priimak/HaasoscopePro/sub boards/eval board/DC041A_ADC12DL3200EVM-ASY.pdf

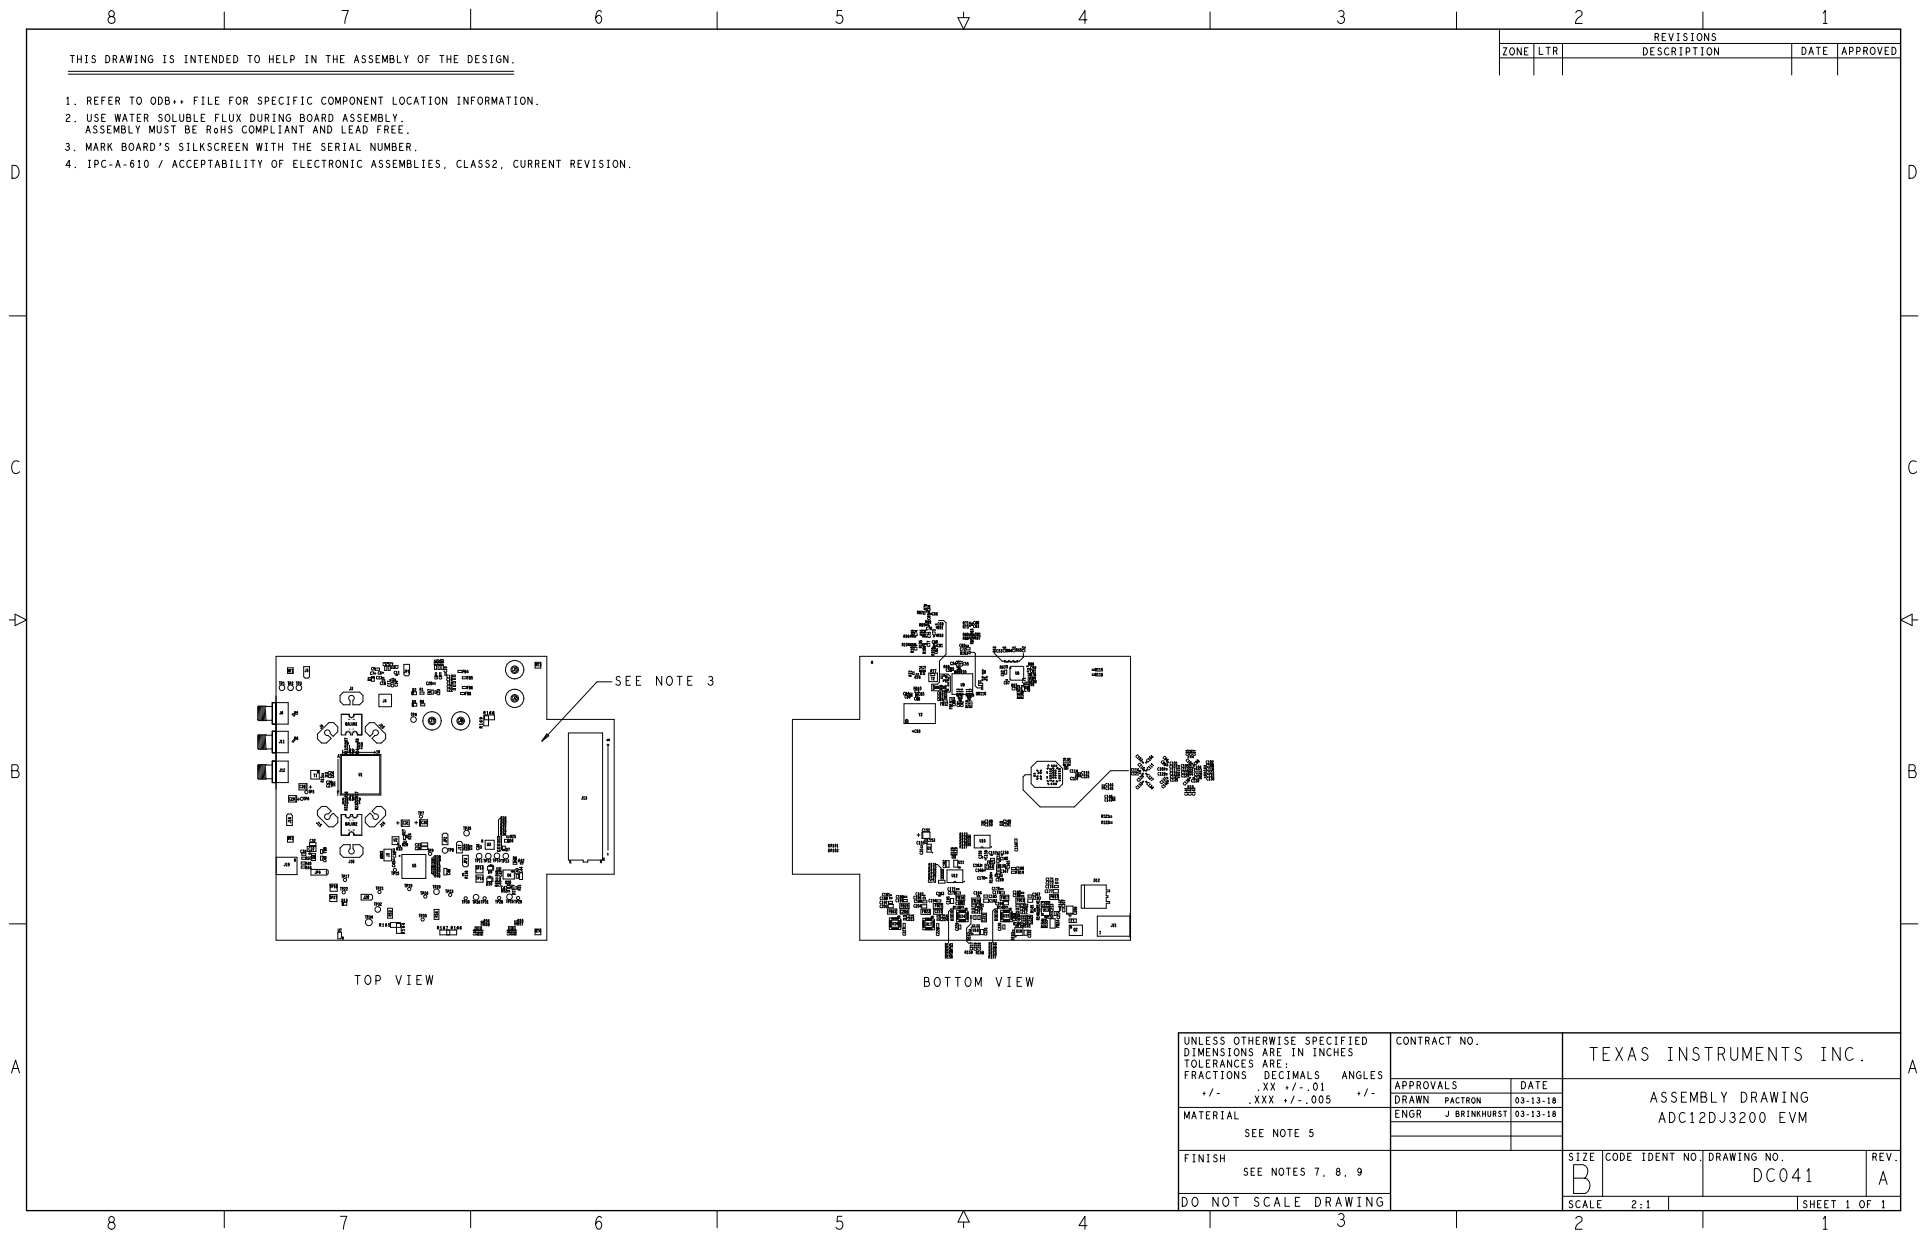
[picture p21: page 1]
