priimak/HaasoscopePro/sub boards/eval board/DC041A_ADC12DL3200EVM-FAB.pdf

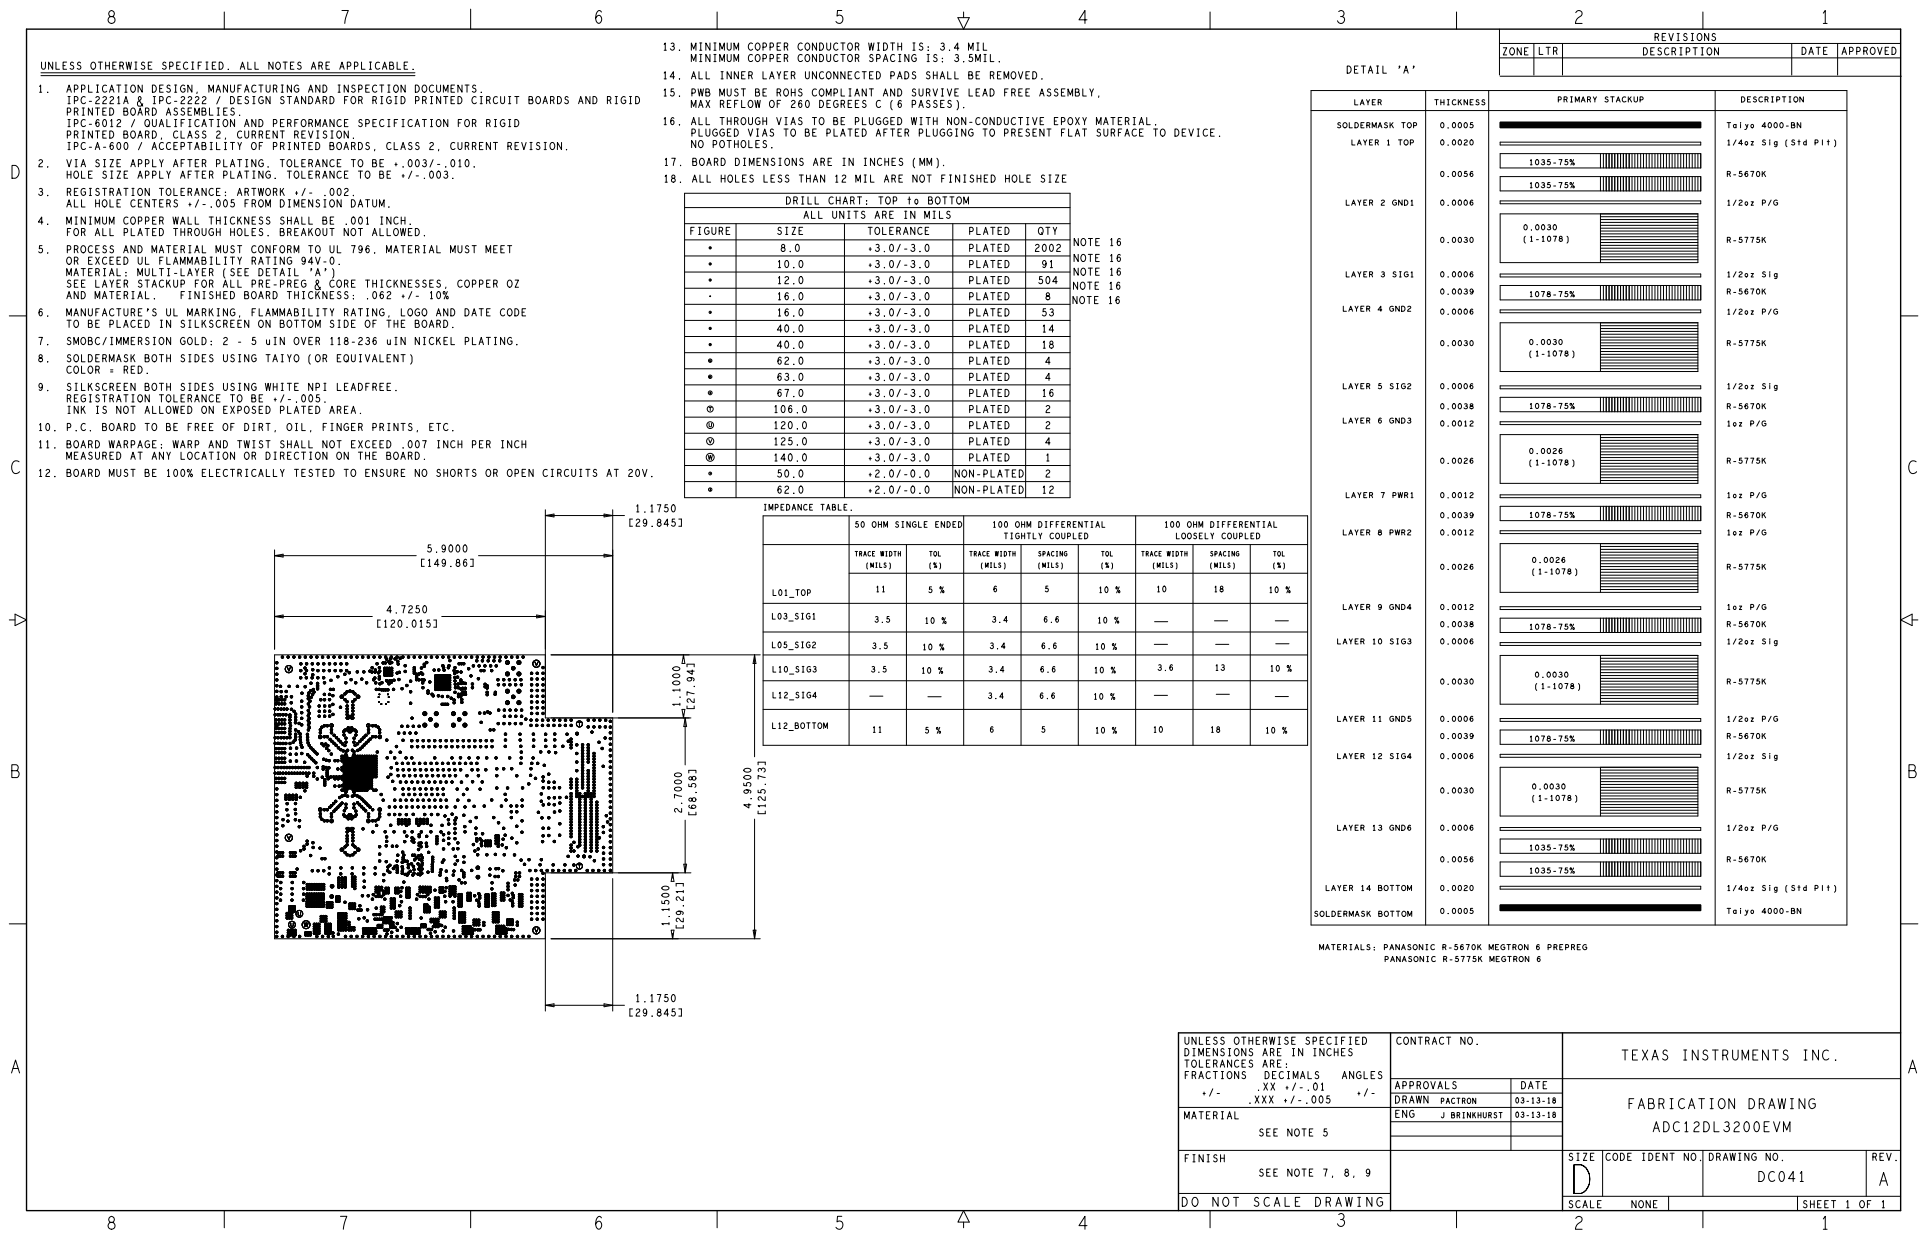
[picture p22: page 1]
