priimak/HaasoscopePro/sub boards/eval board/DC041A_ADC12DL3200EVM-LYR.pdf

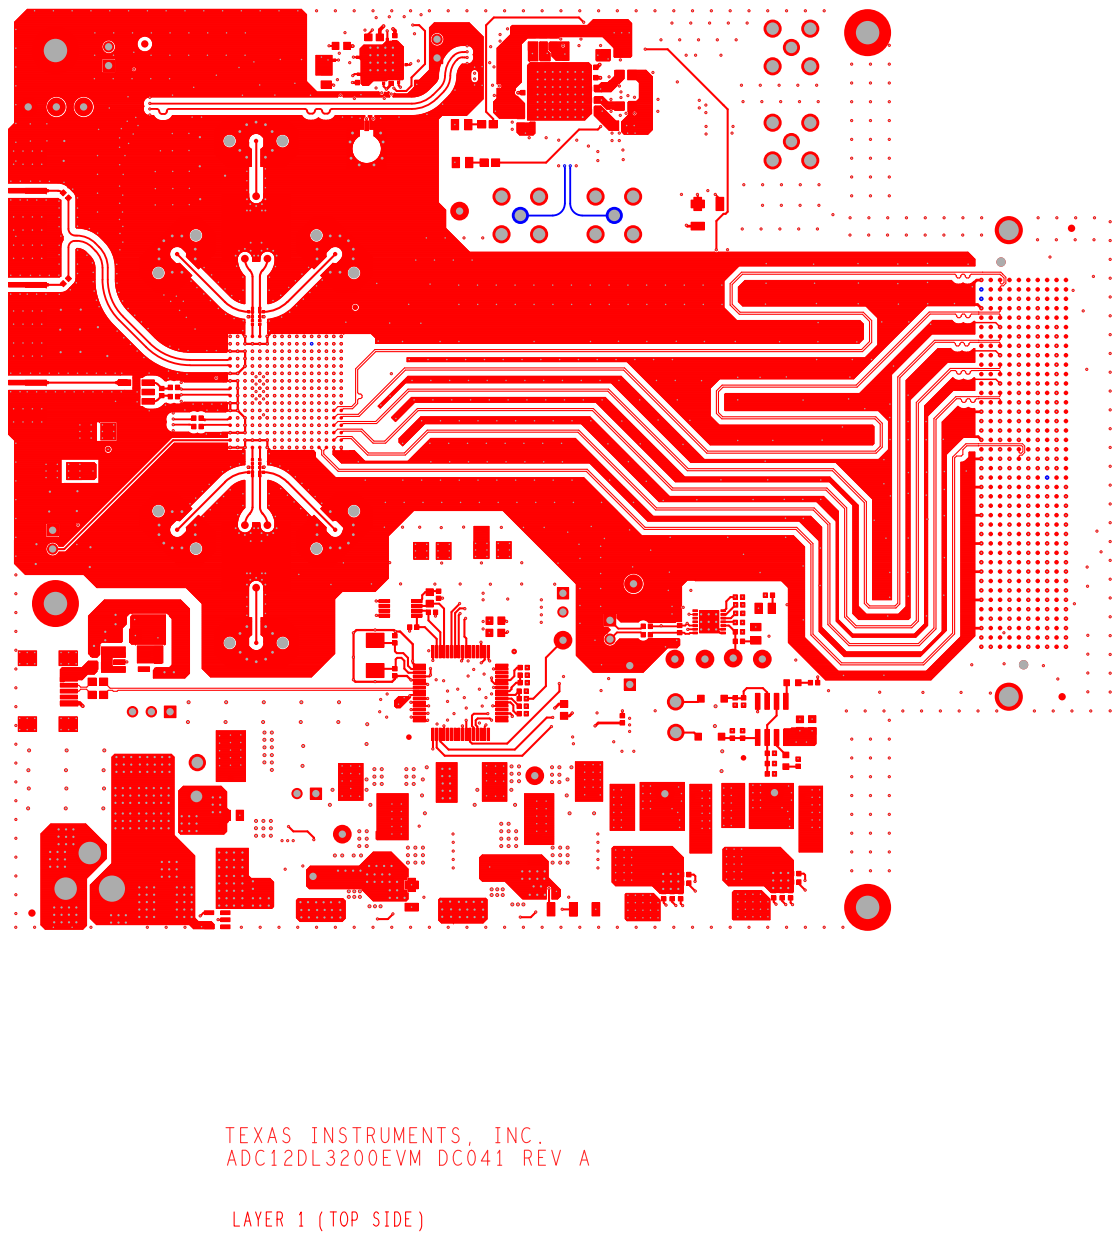
[picture p23: page 1]

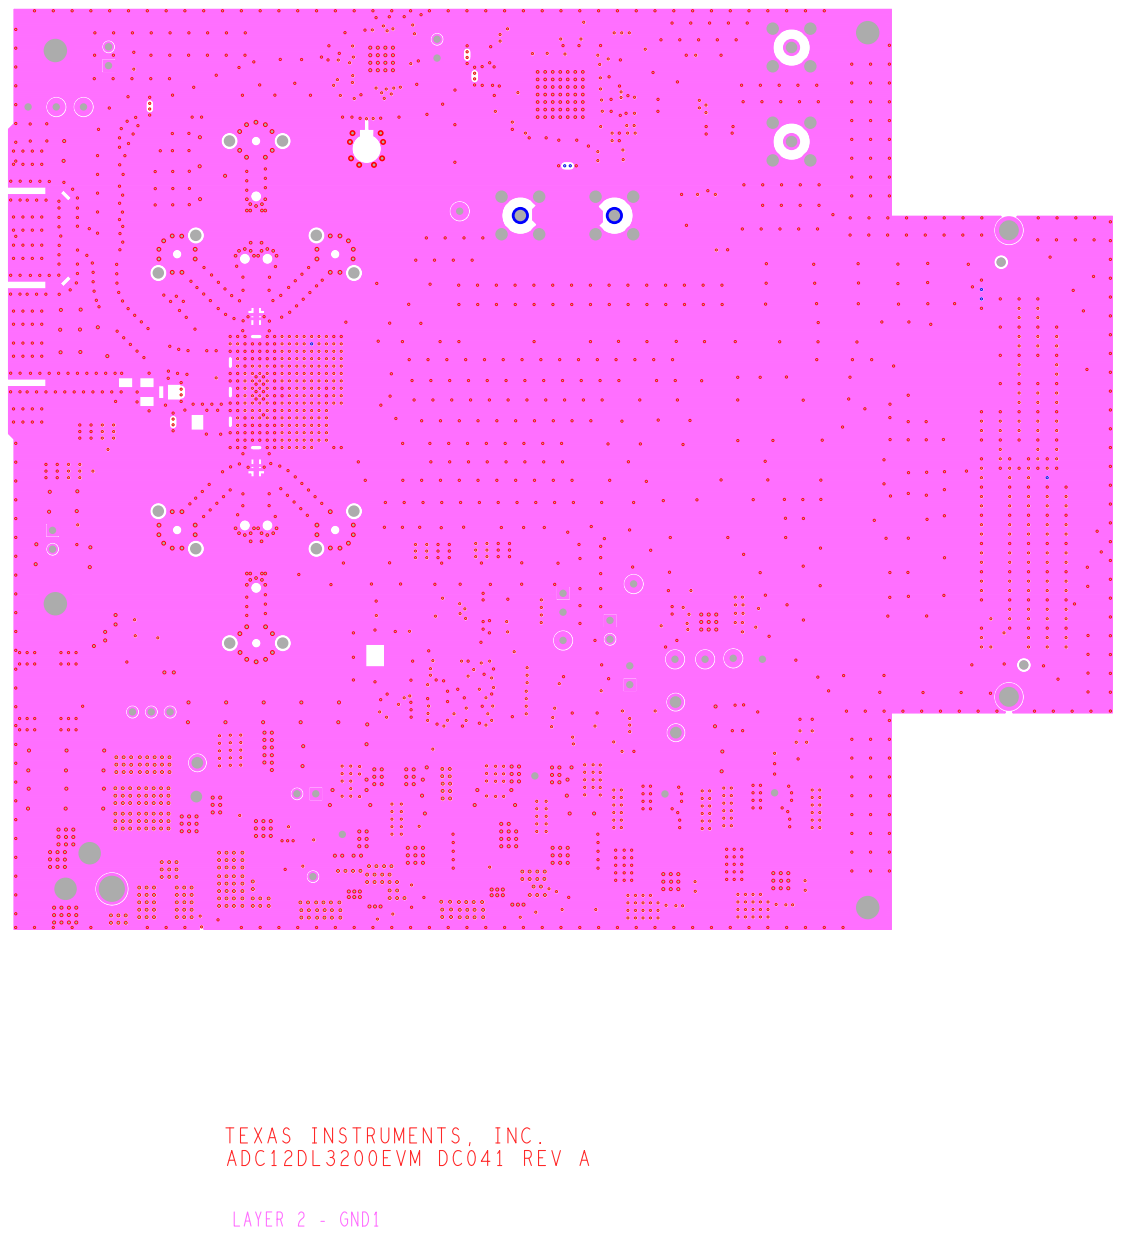
[picture p24: page 2]

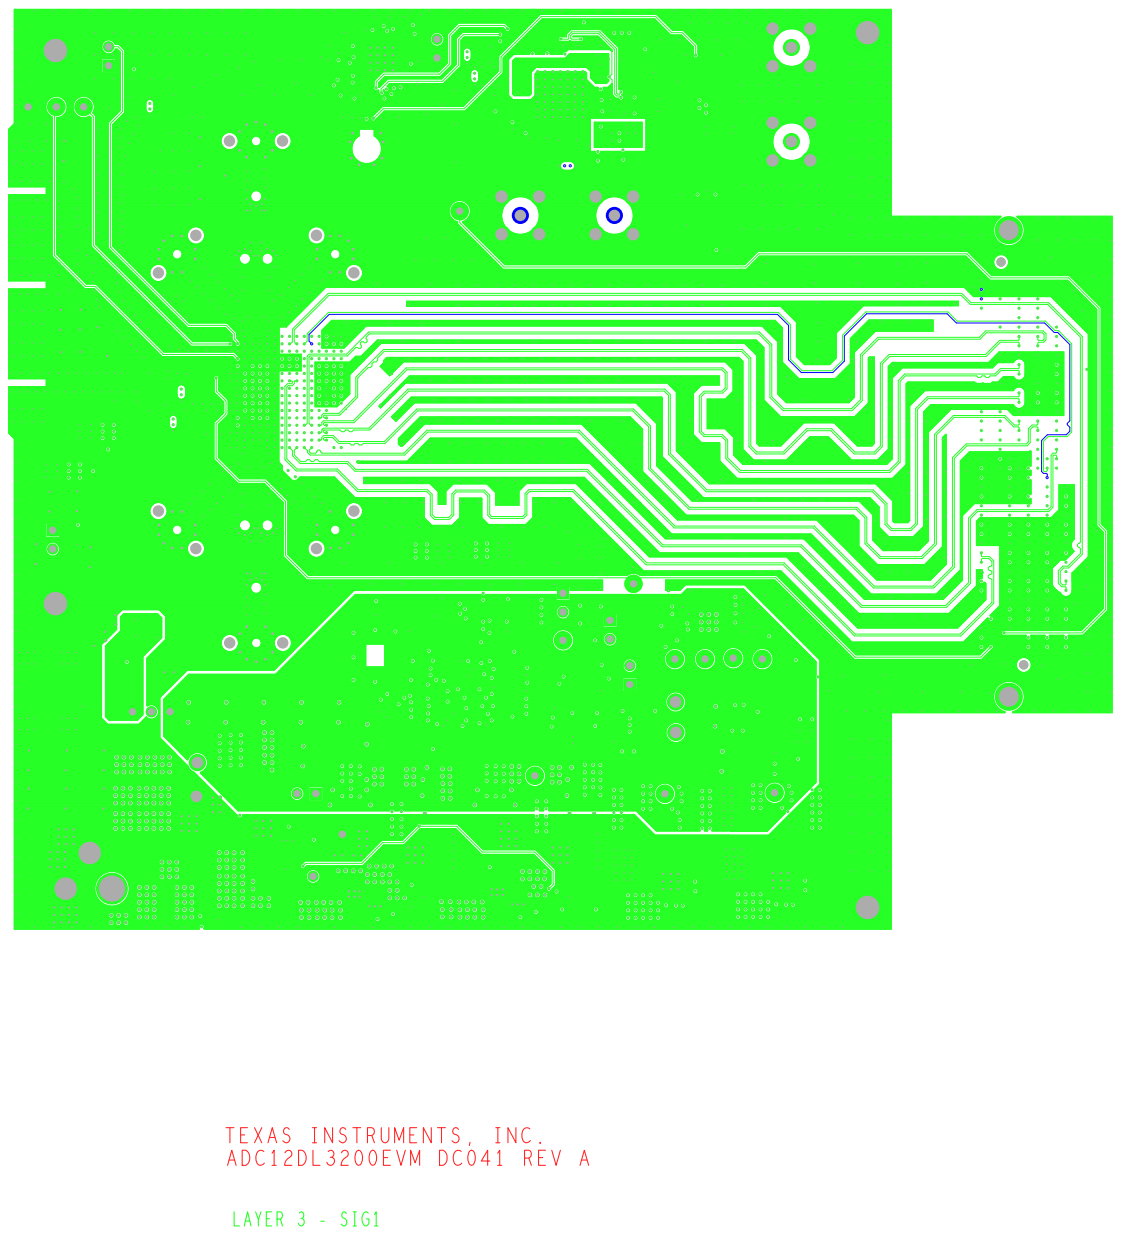
[picture p25: page 3]

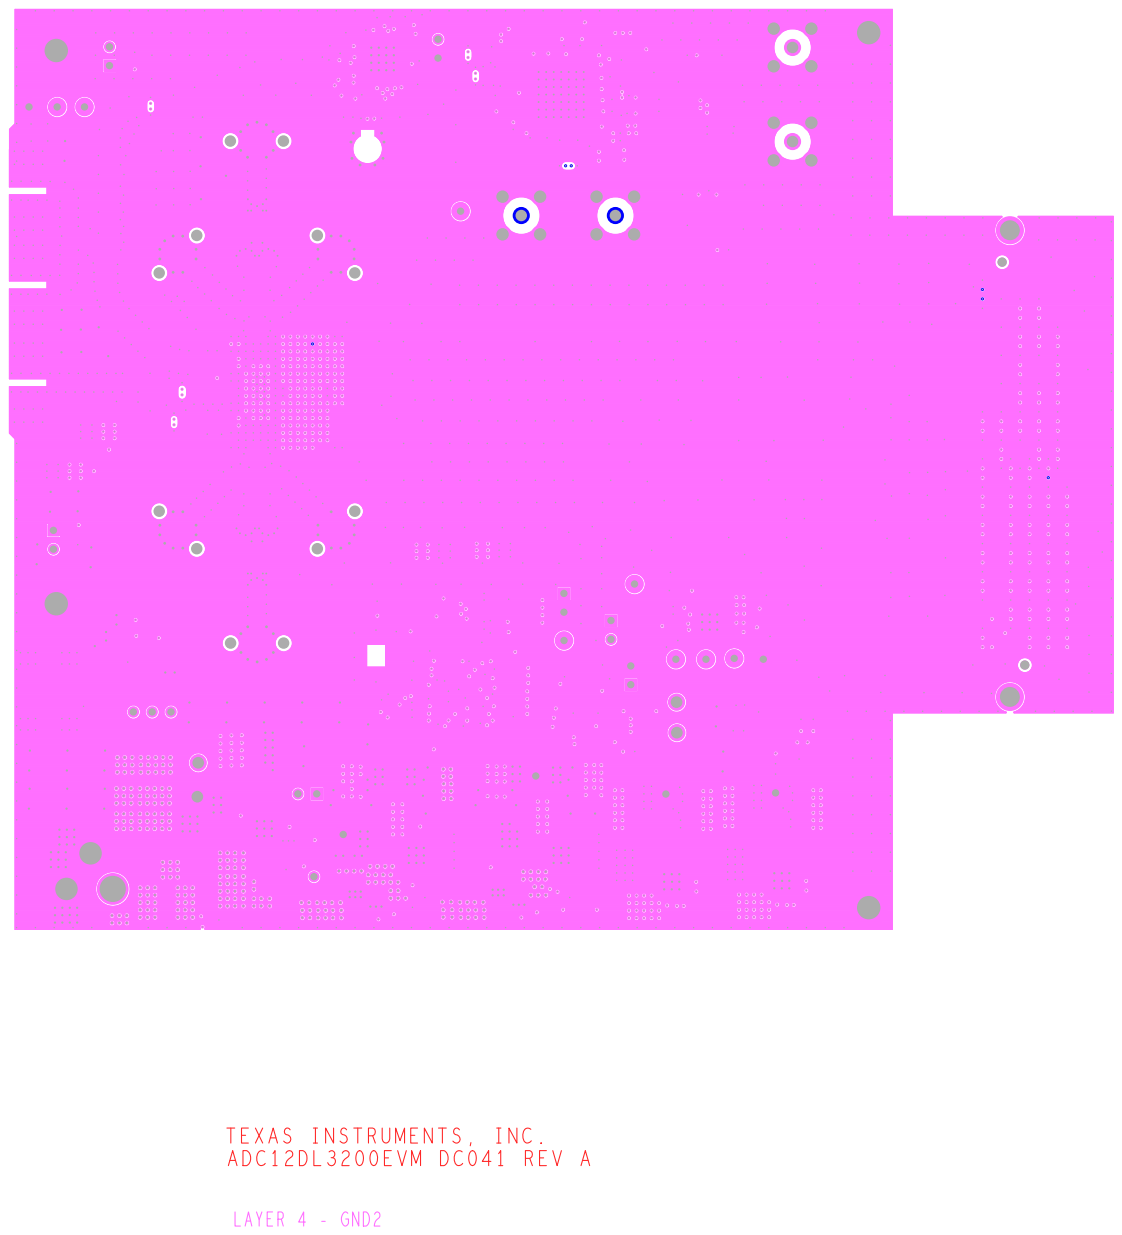
[picture p26: page 4]

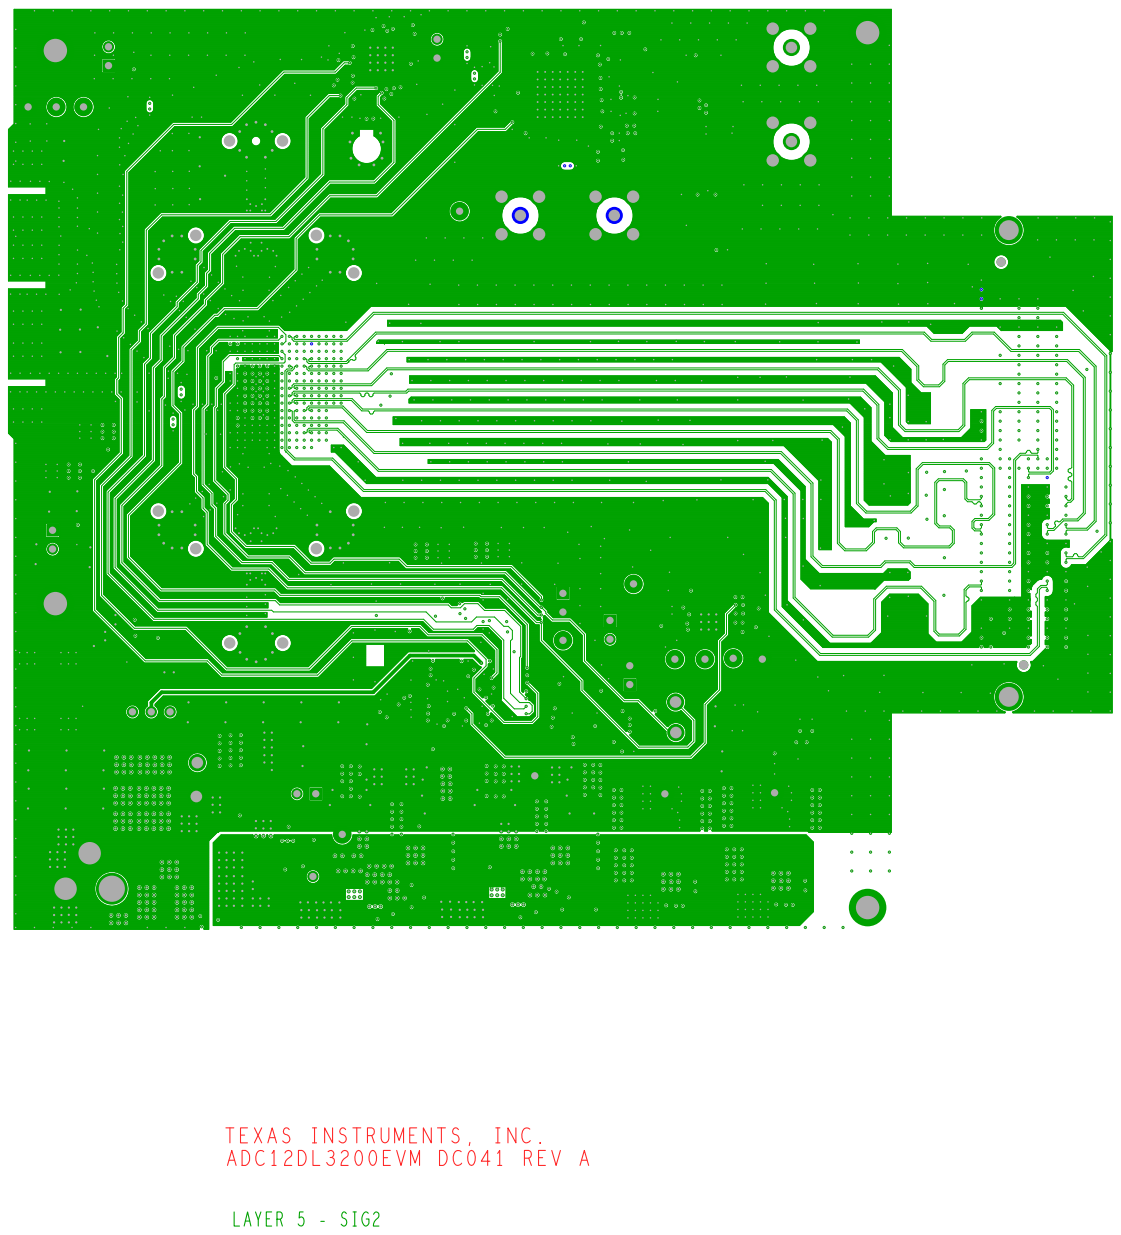
[picture p27: page 5]

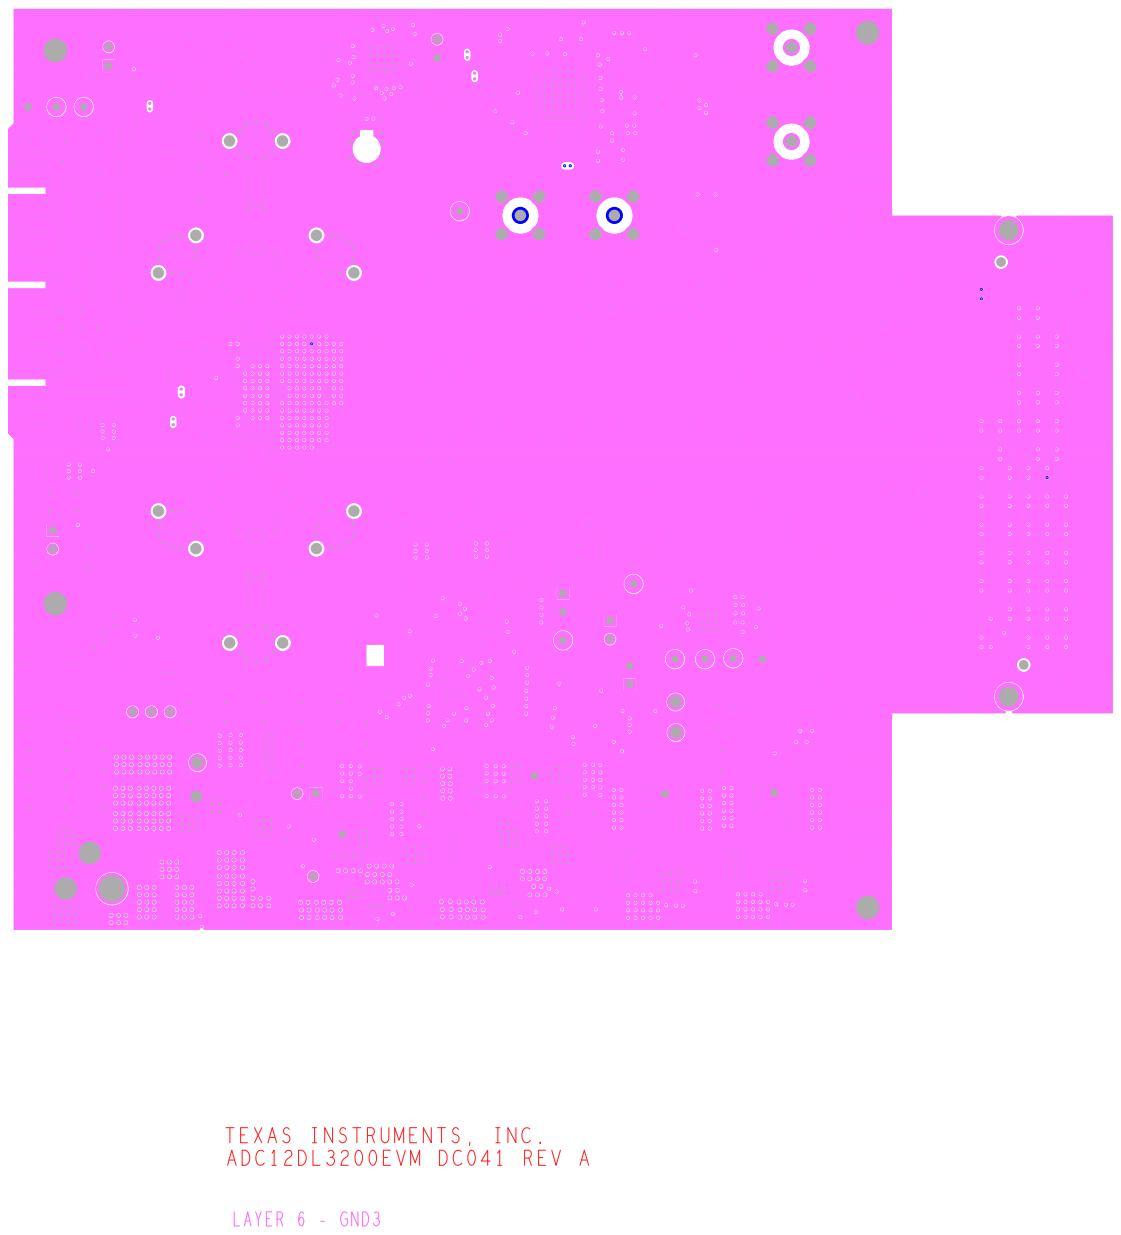
[picture p28: page 6]

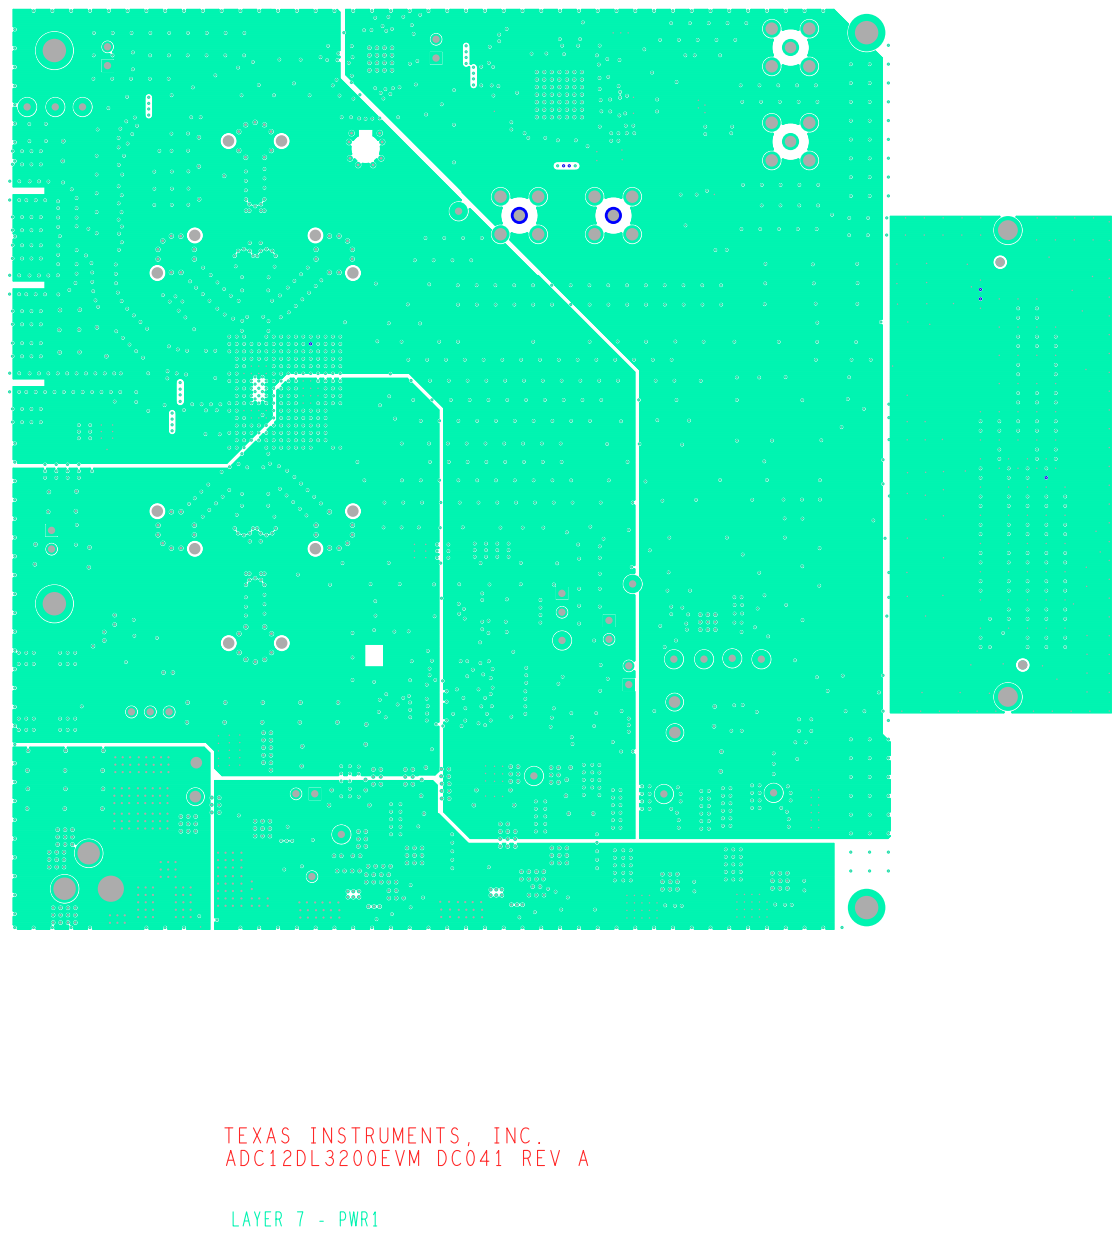
[picture p29: page 7]

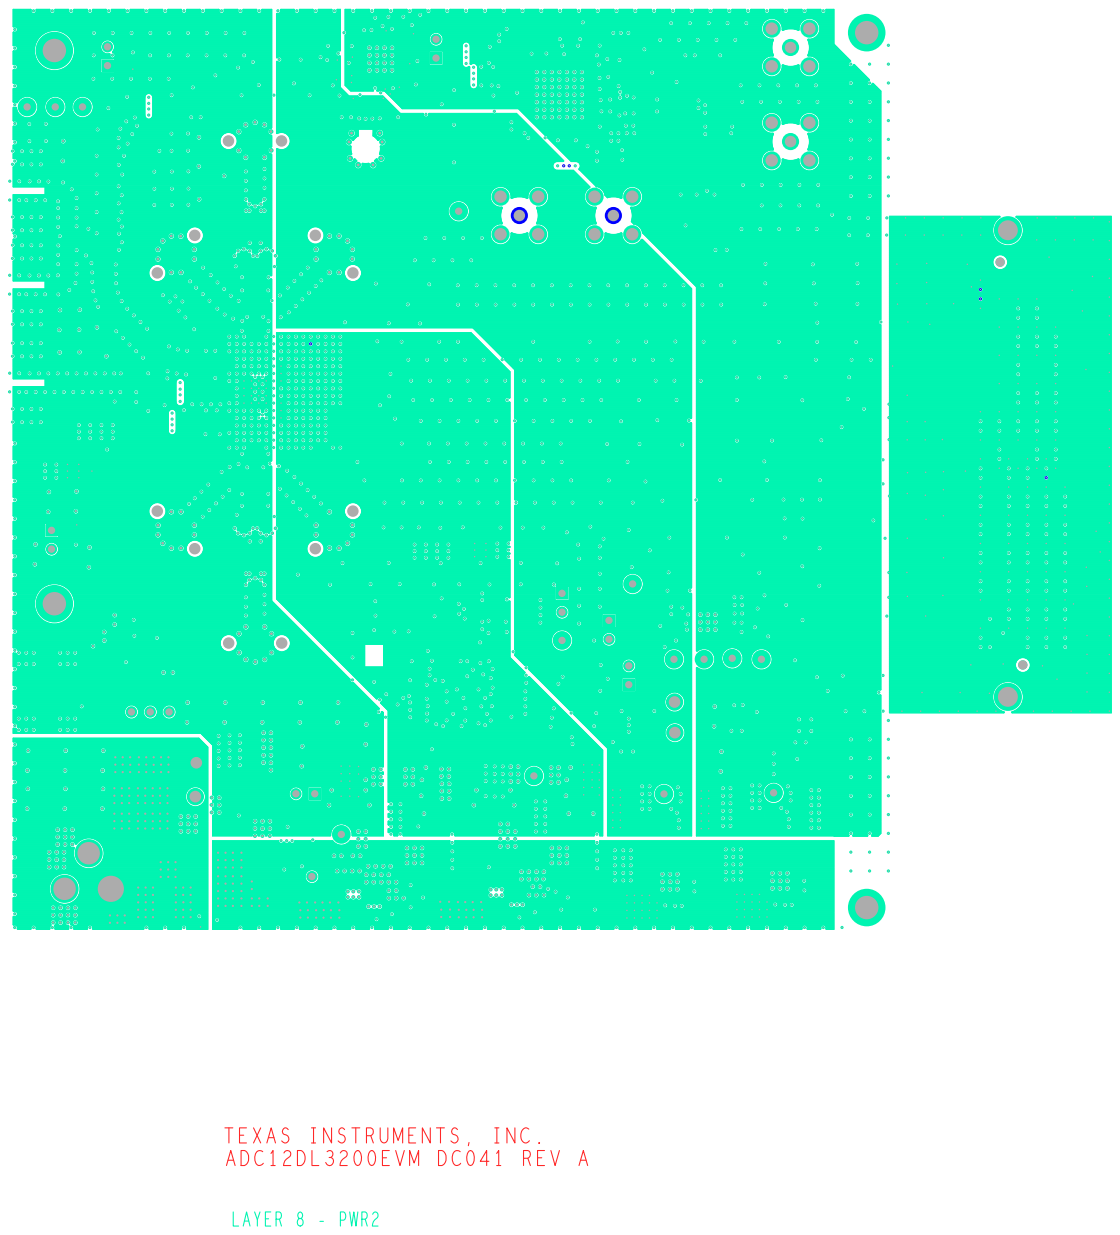
[picture p30: page 8]

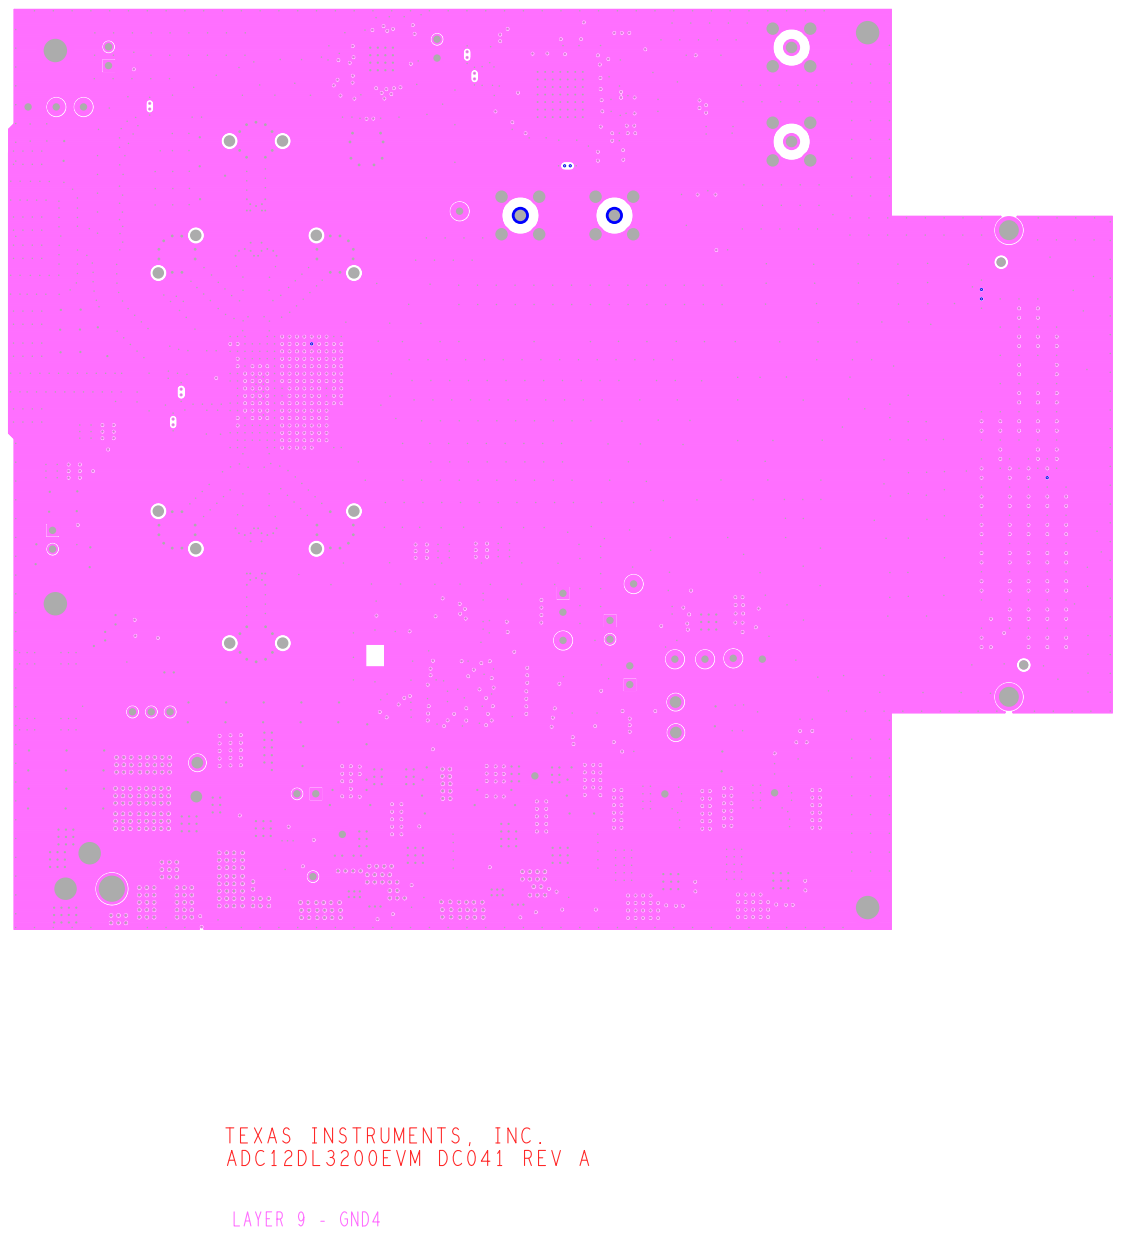
[picture p31: page 9]

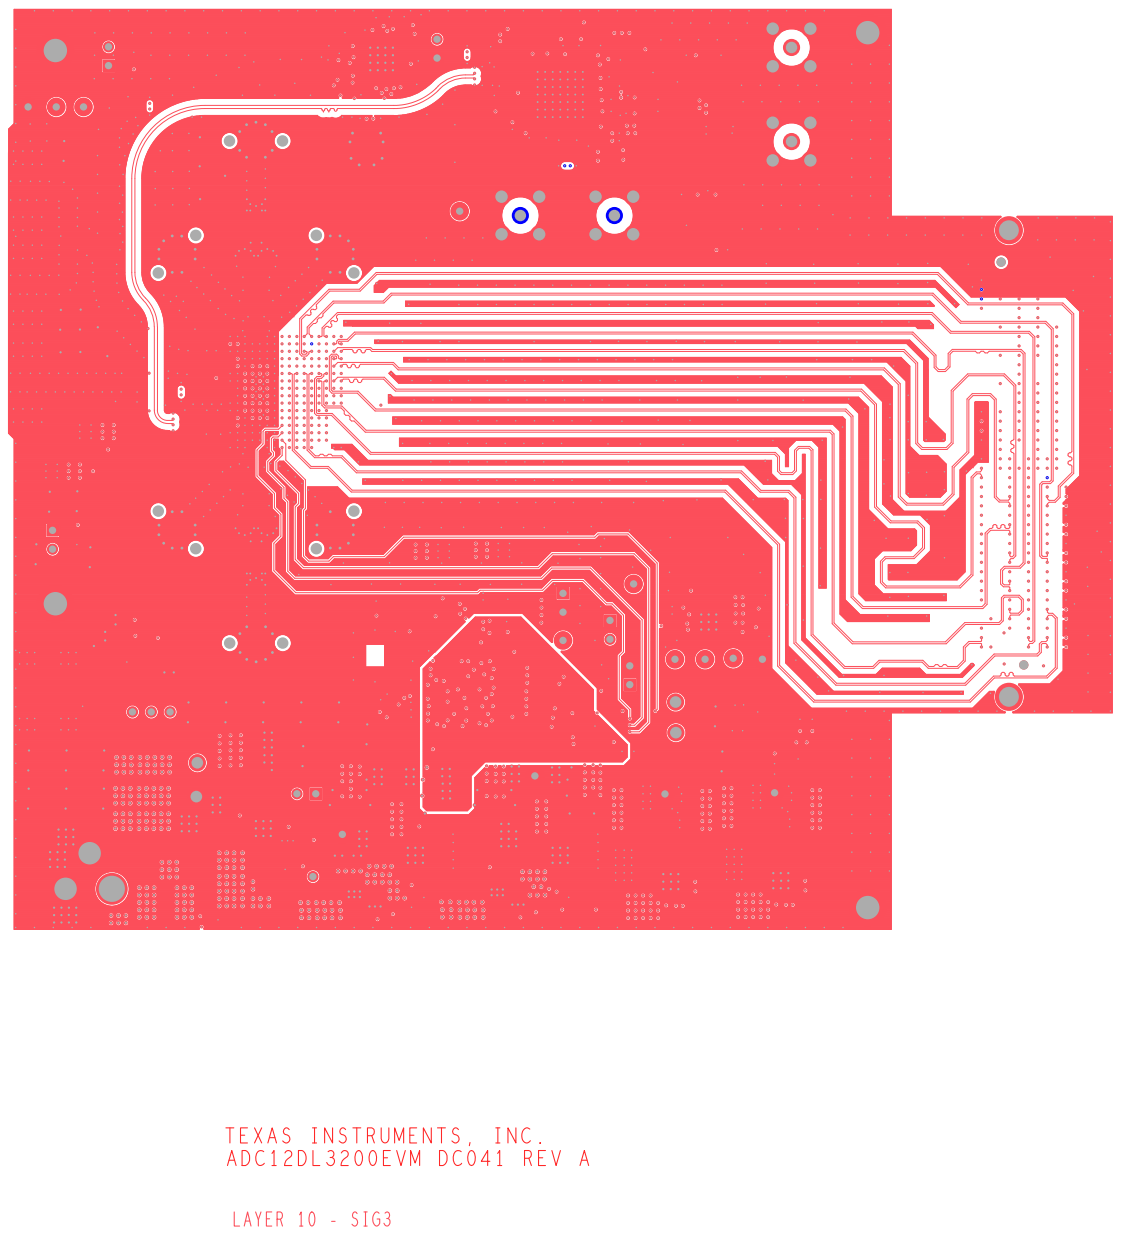
[picture p32: page 10]

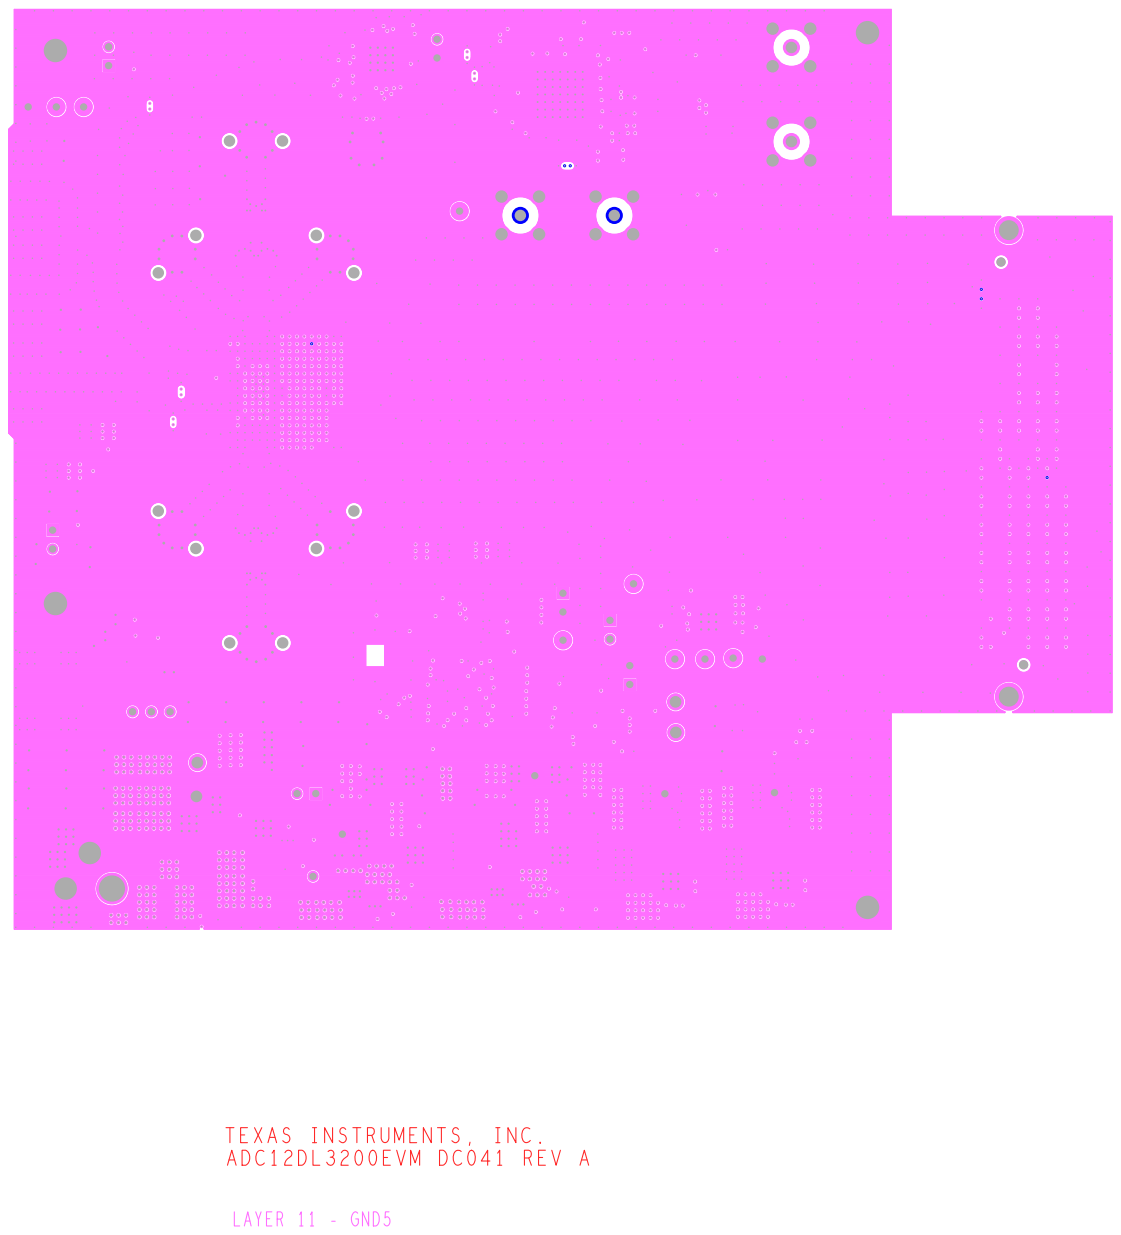
[picture p33: page 11]

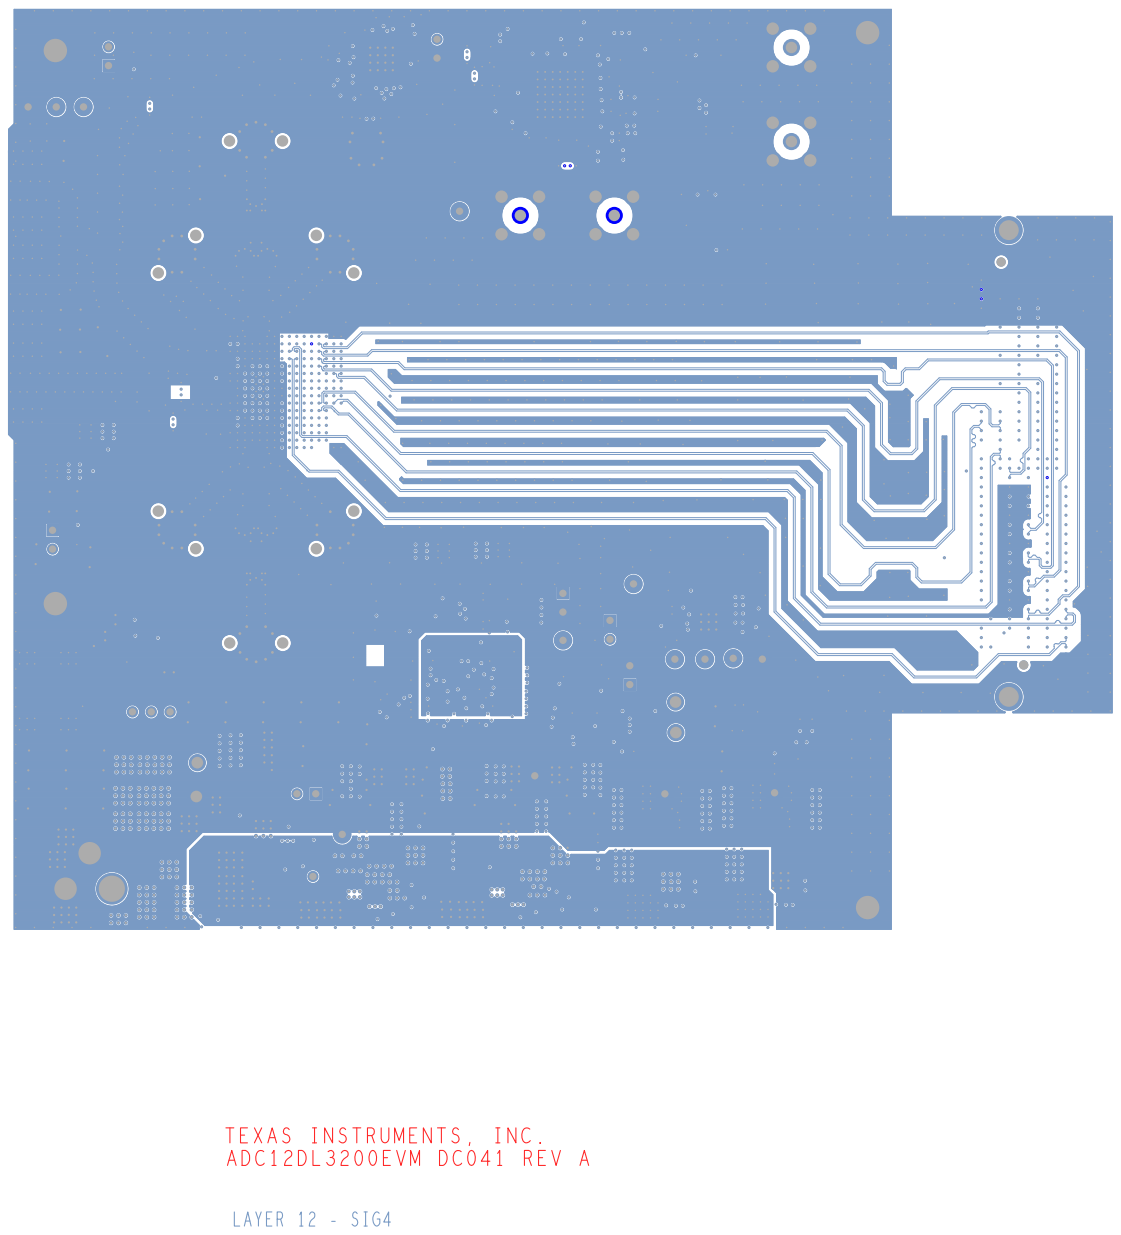
[picture p34: page 12]

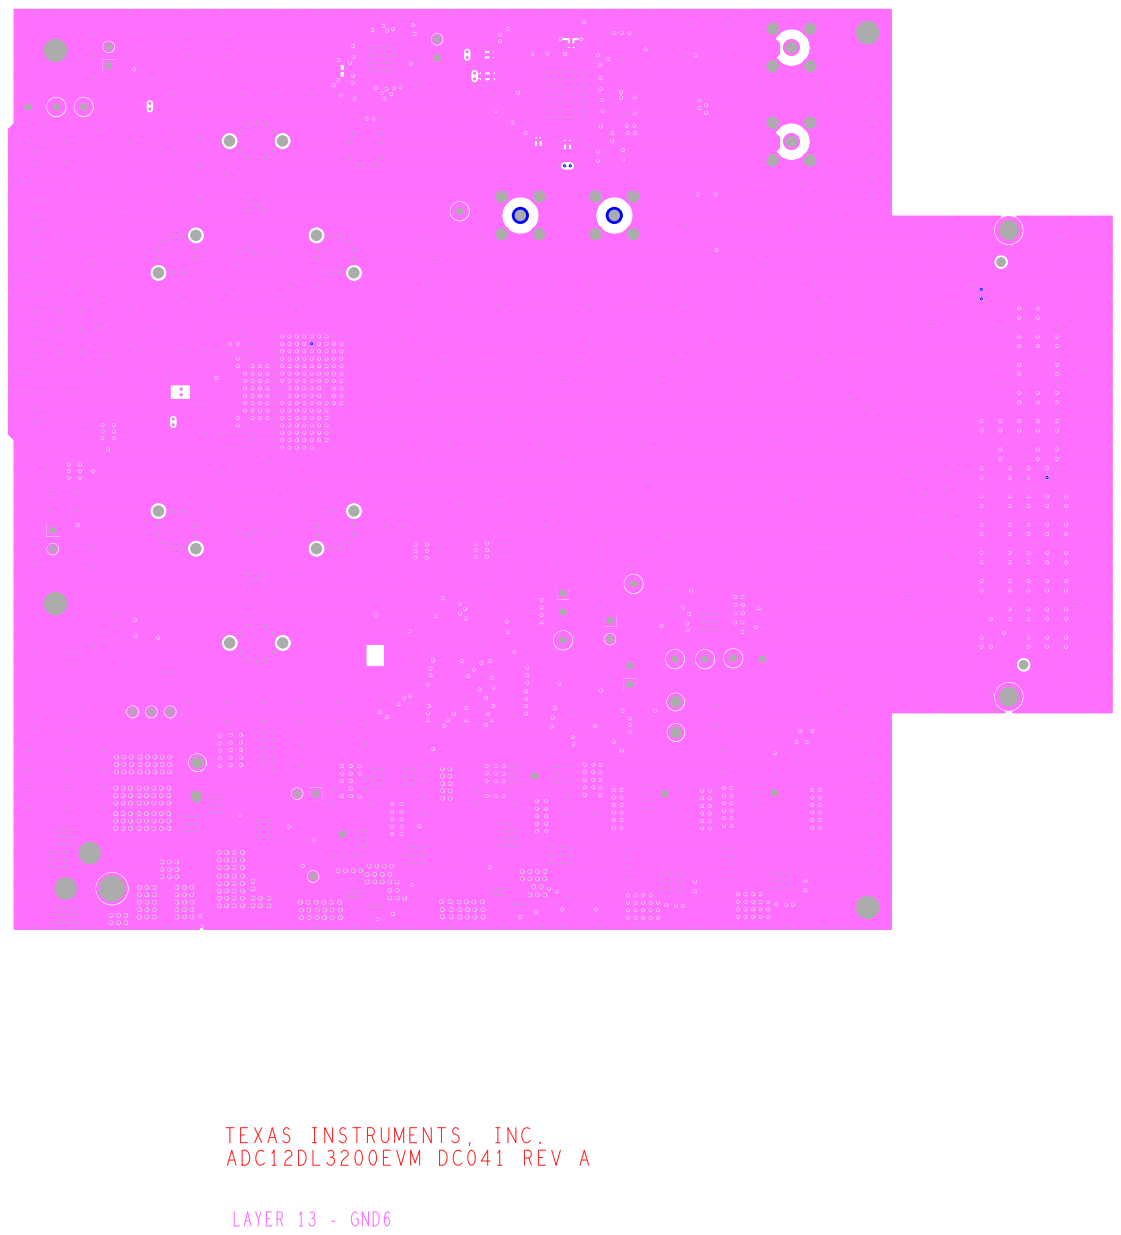
[picture p35: page 13]

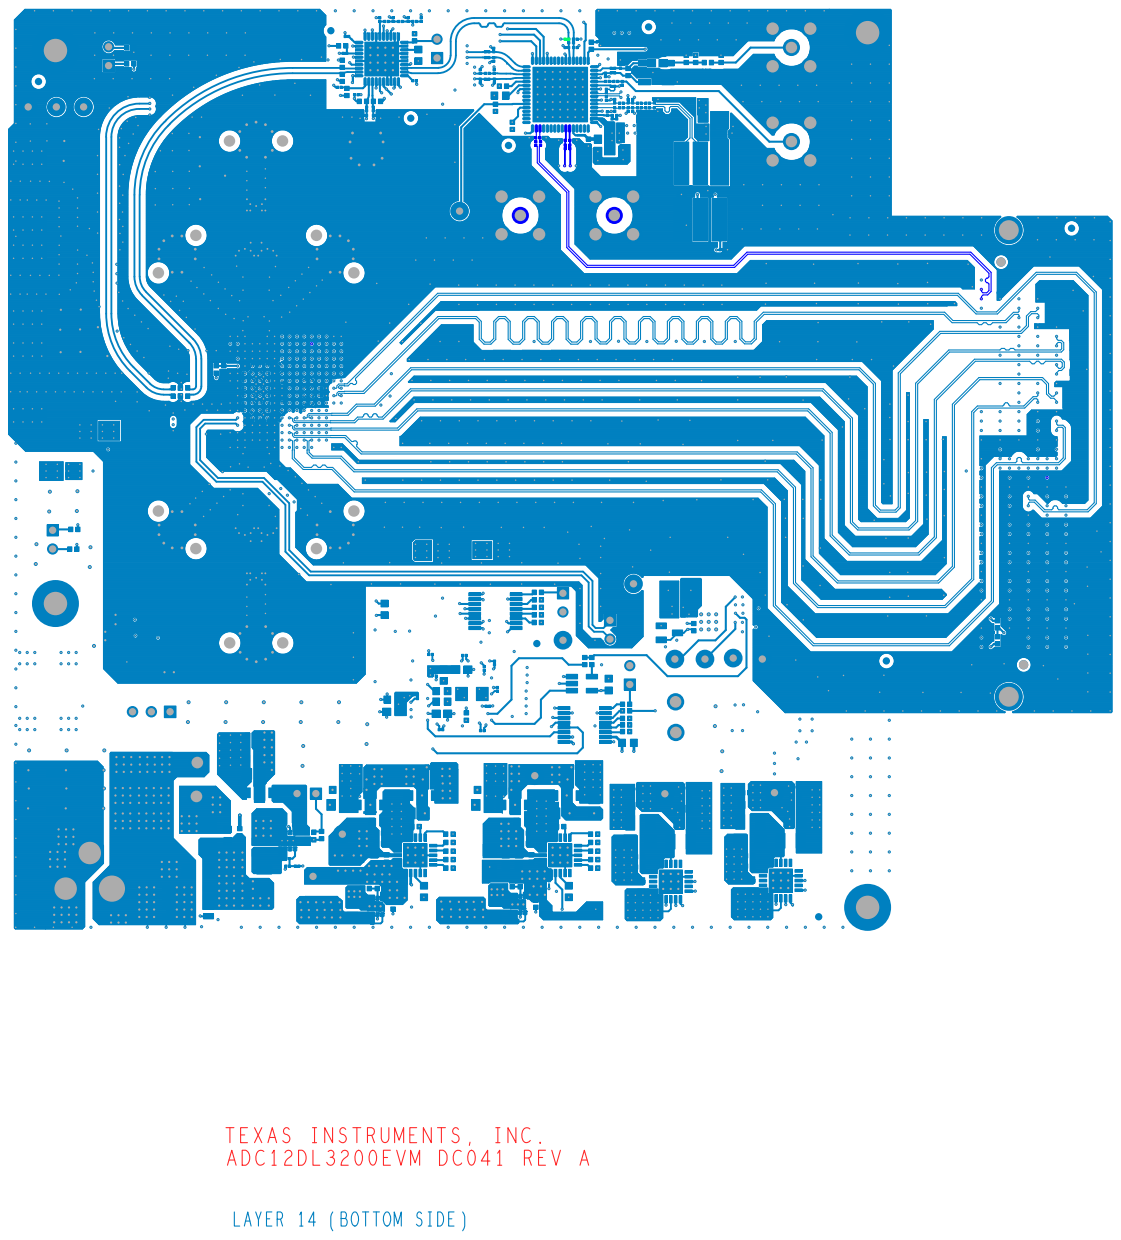
[picture p36: page 14]

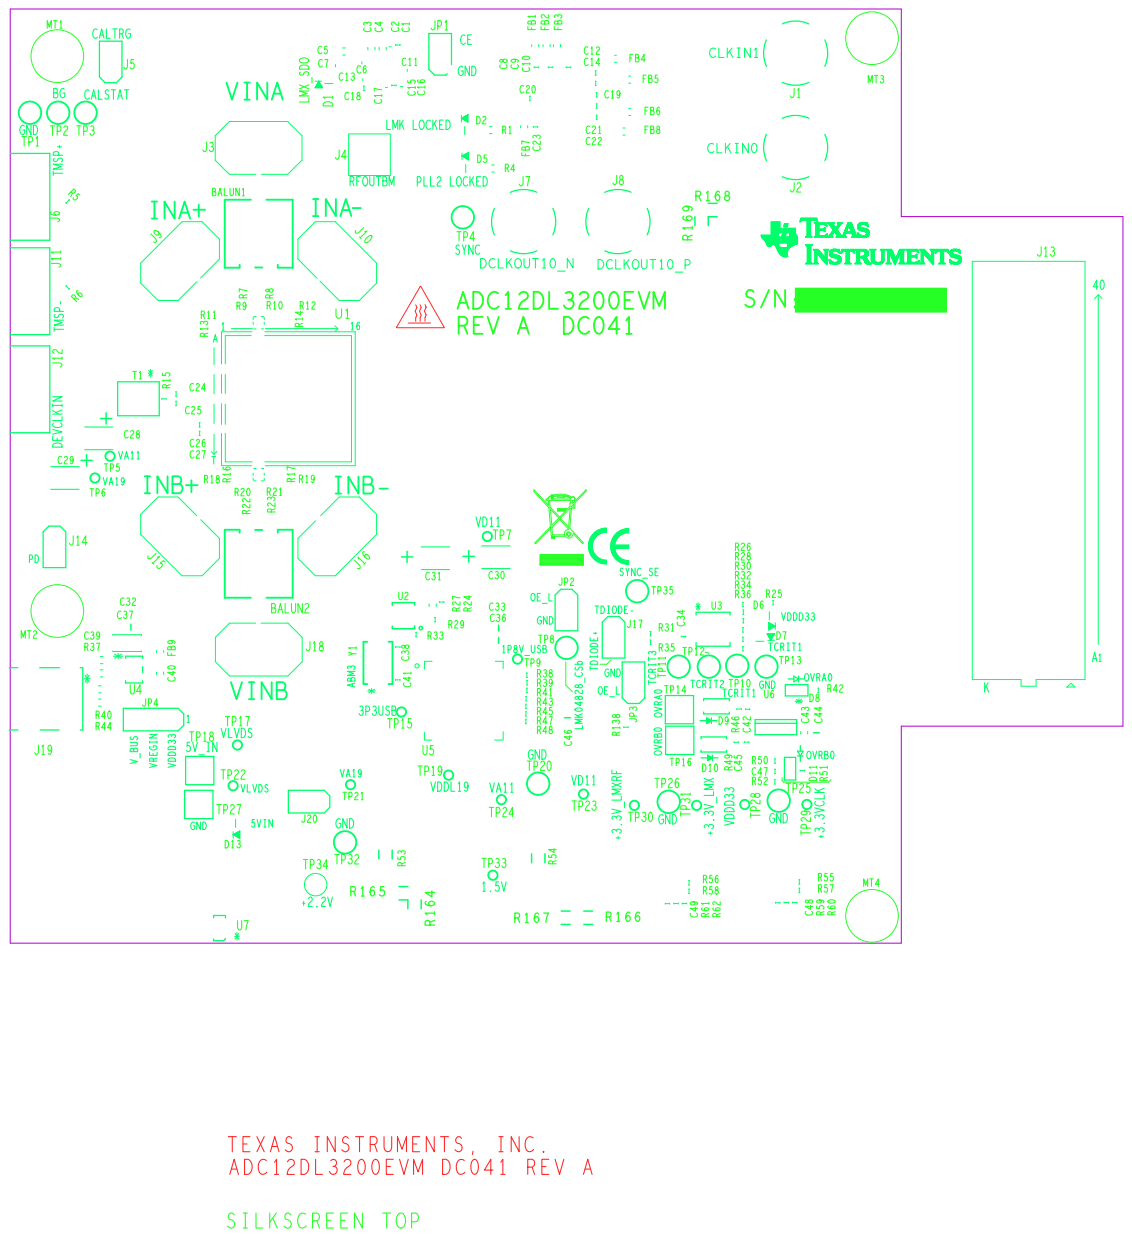
[picture p37: page 15]

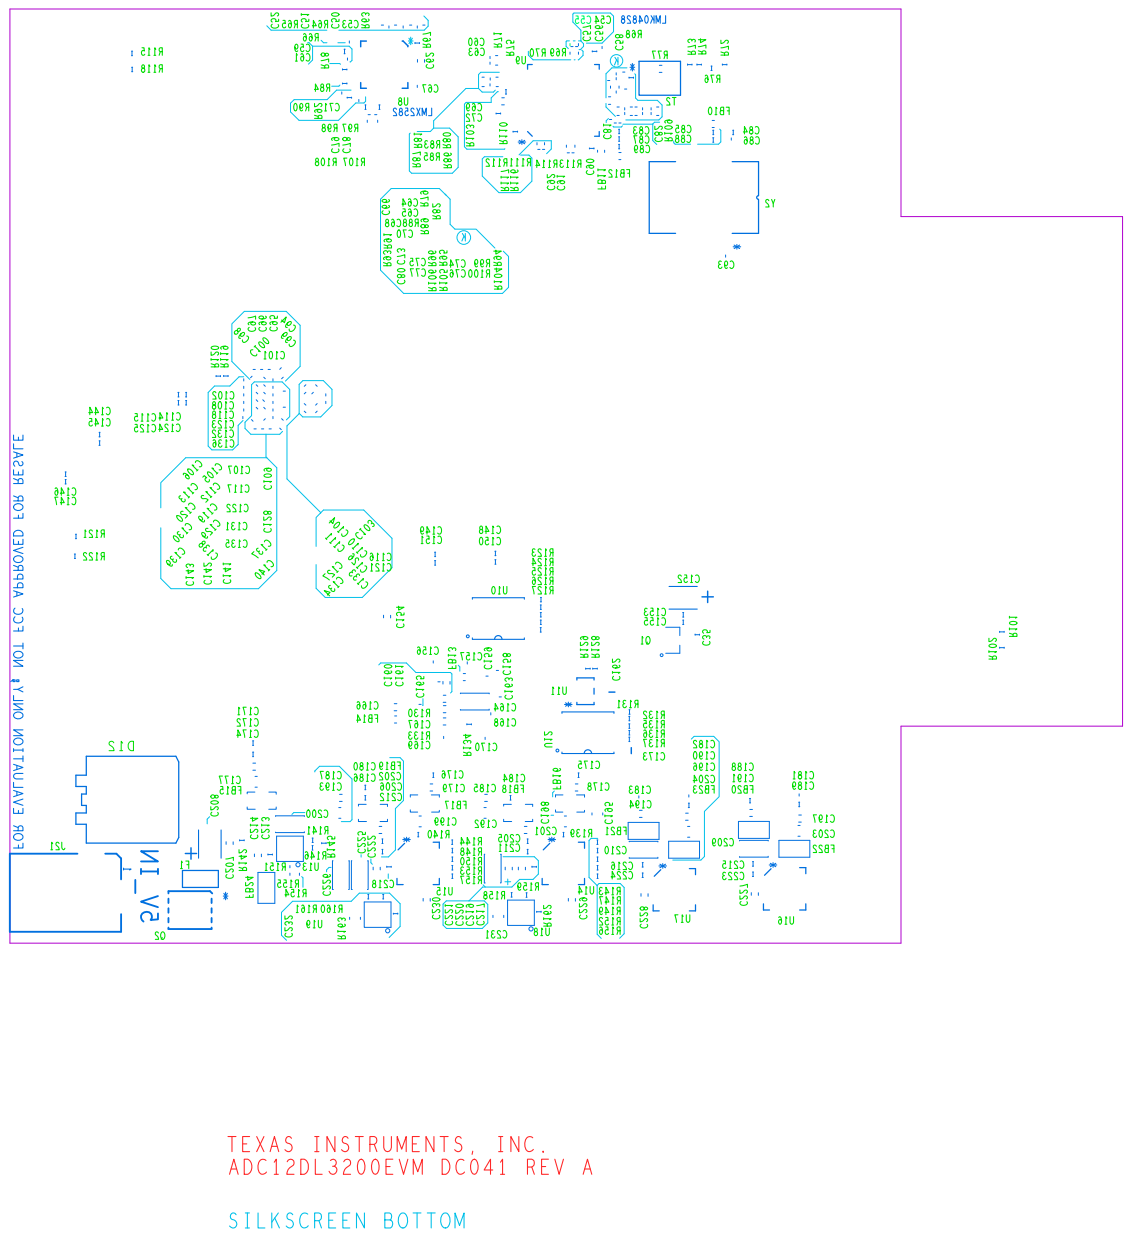
[picture p38: page 16]

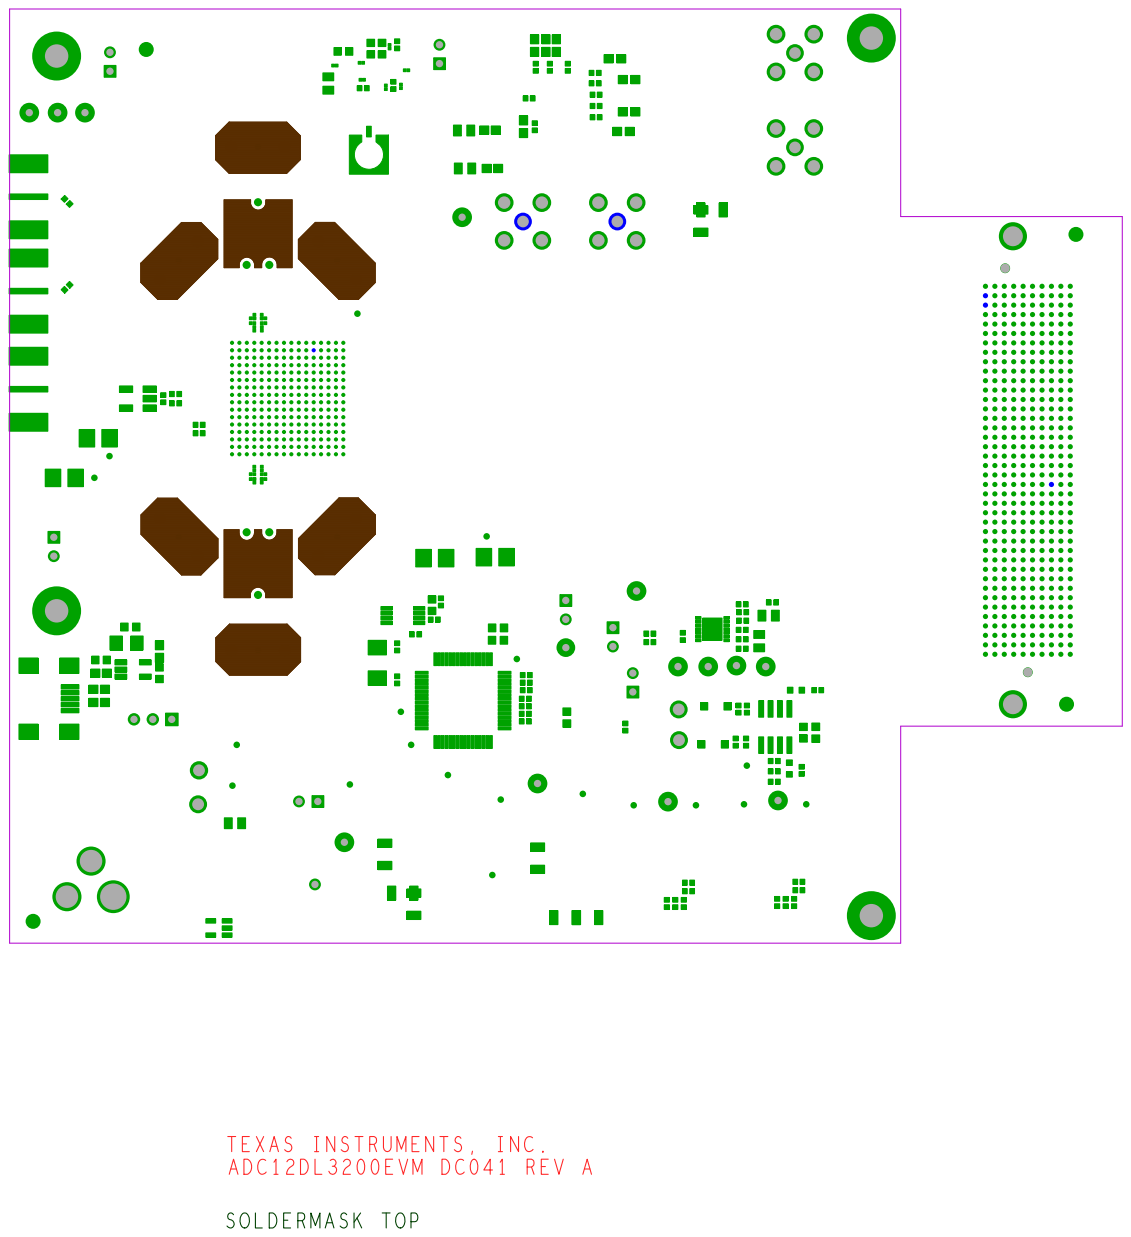
[picture p39: page 17]

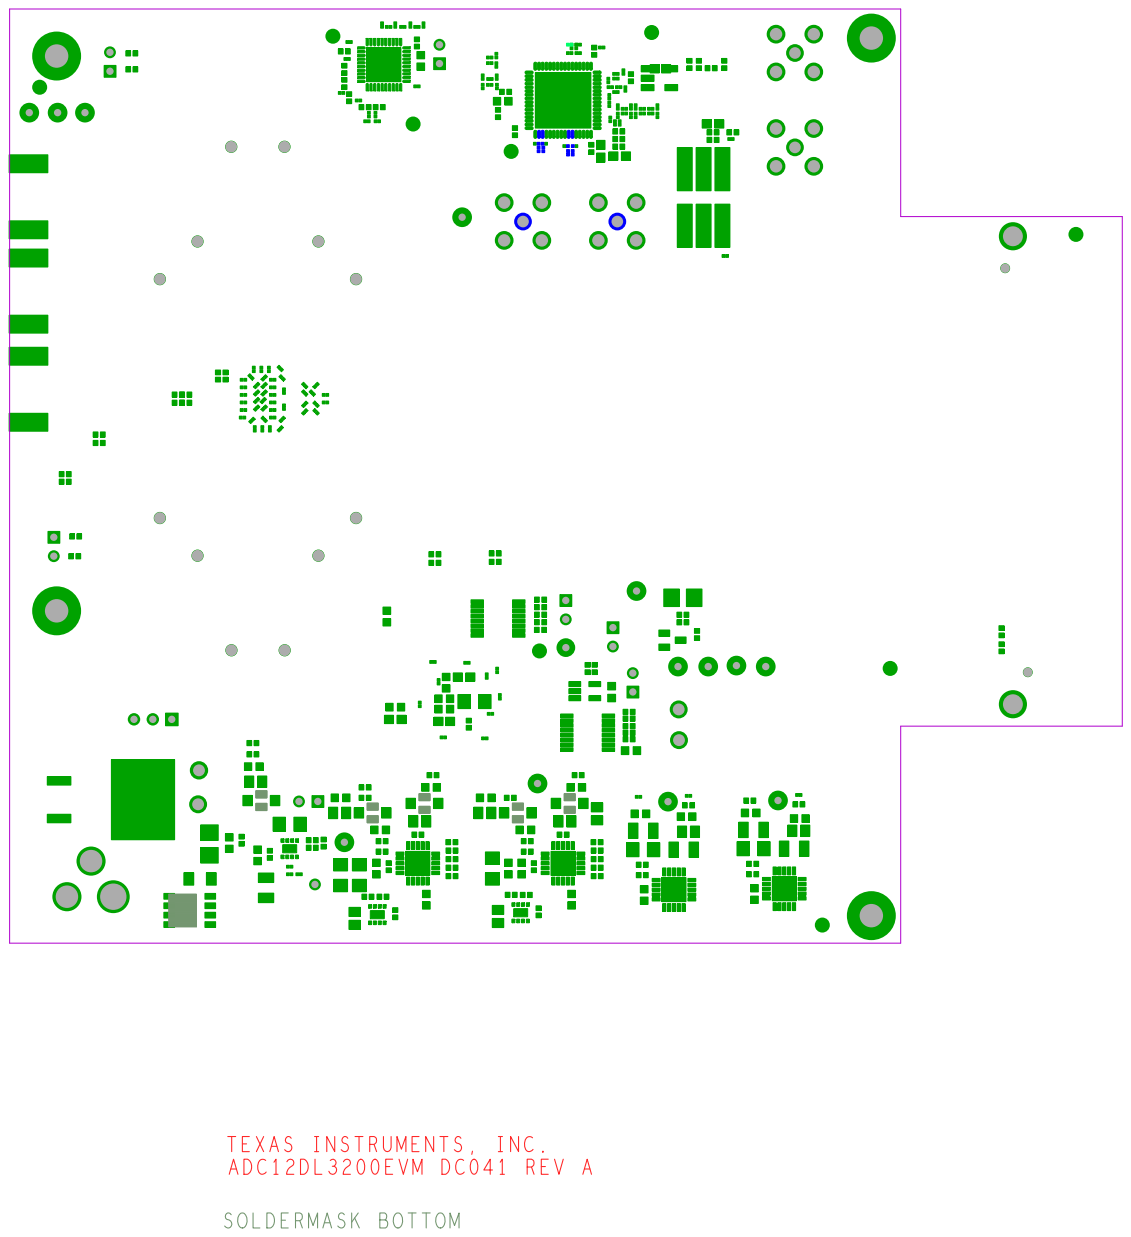
[picture p40: page 18]

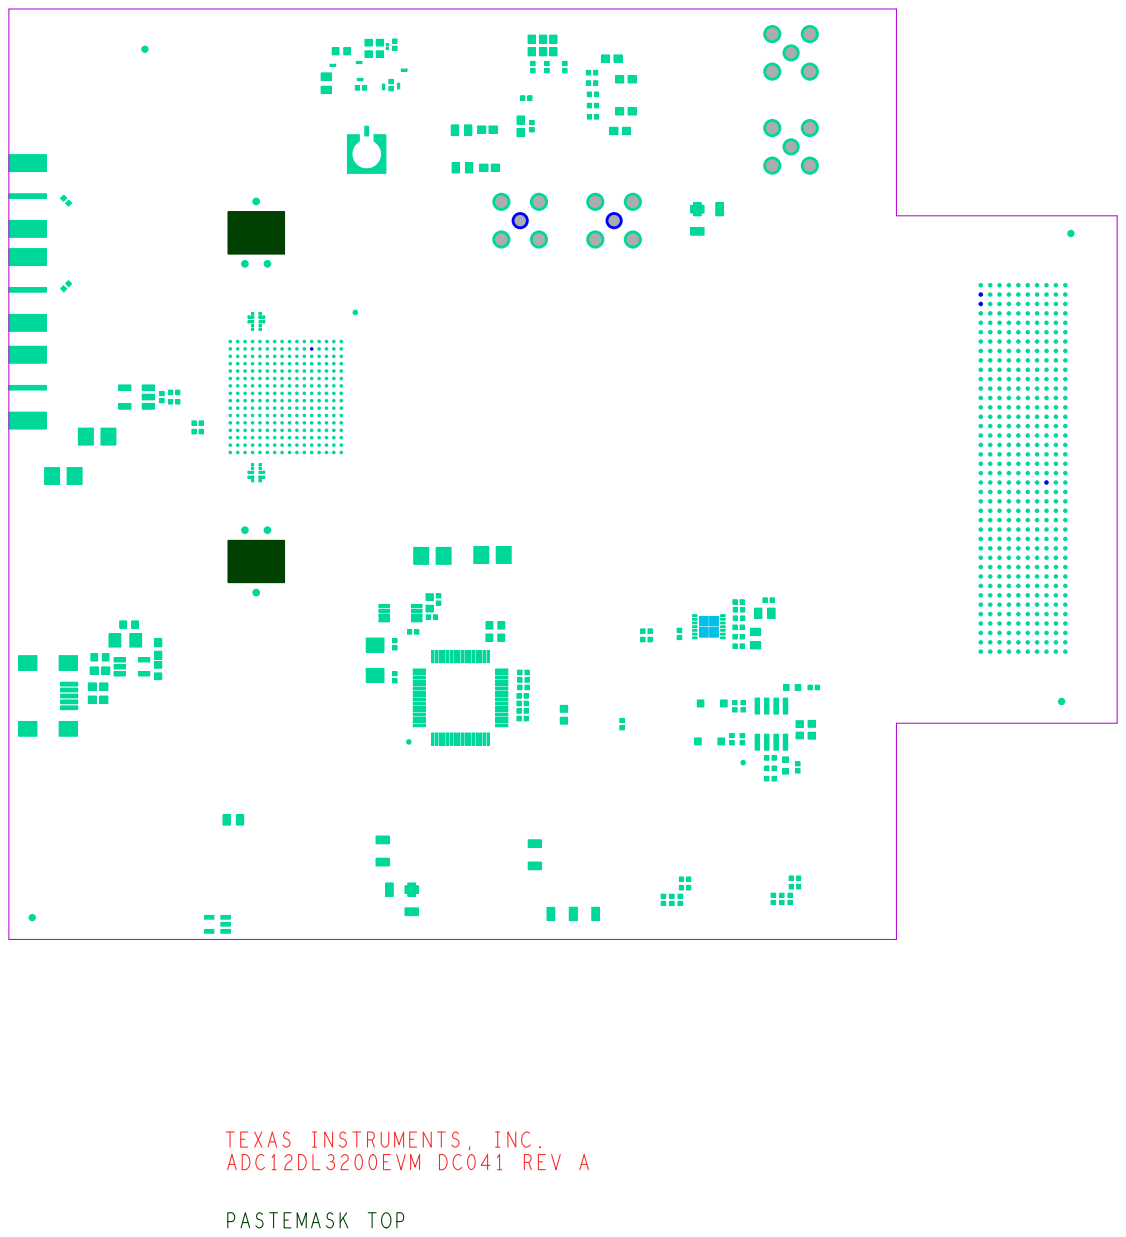
[picture p41: page 19]

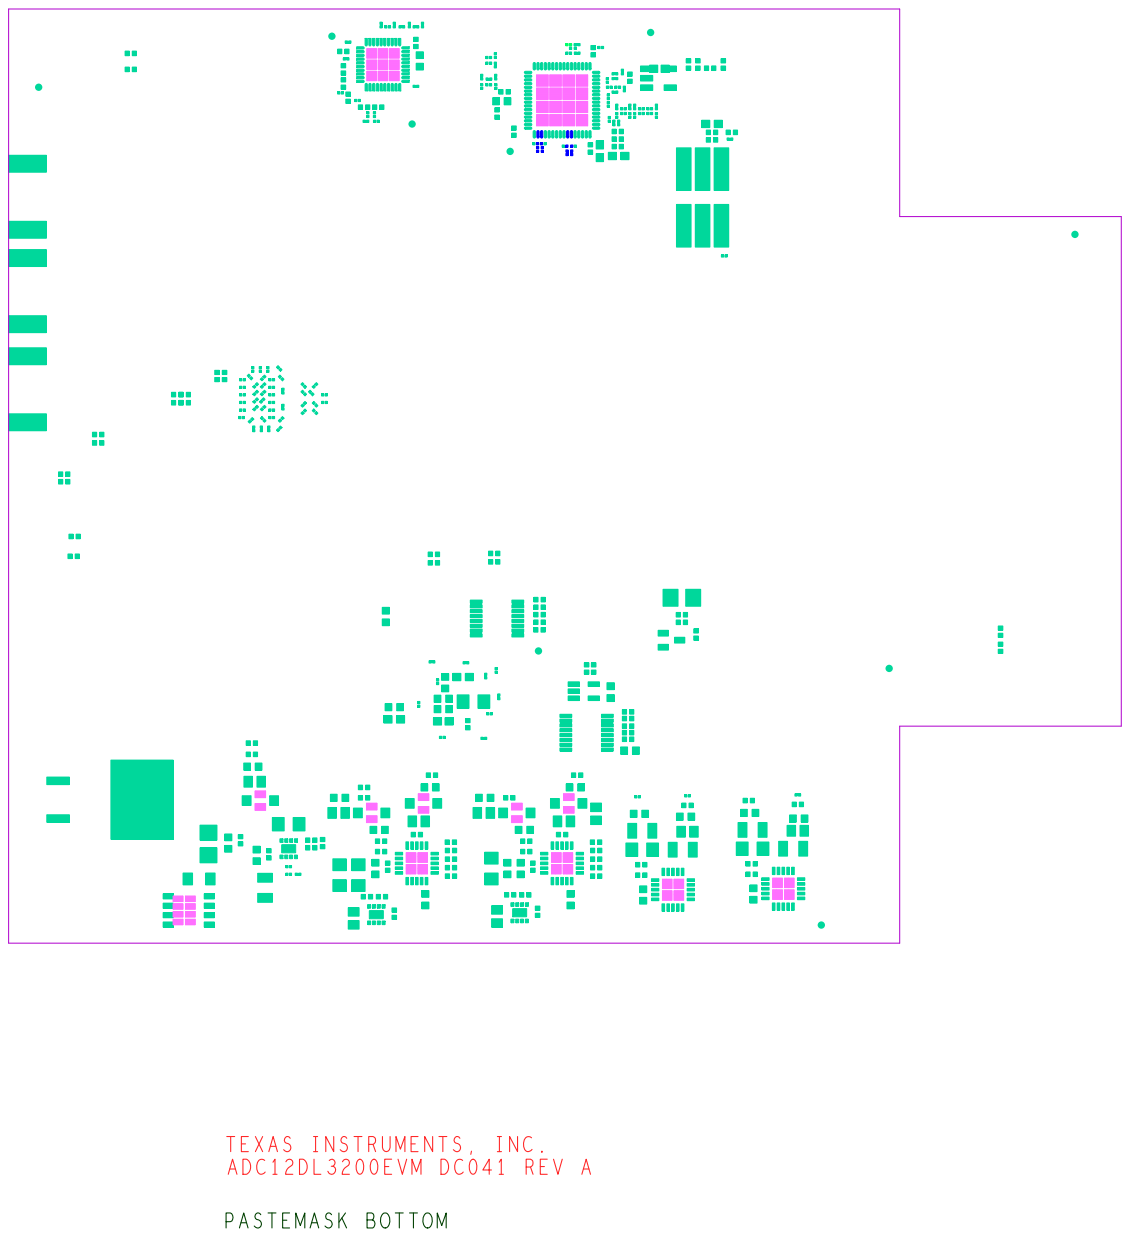
[picture p42: page 20]

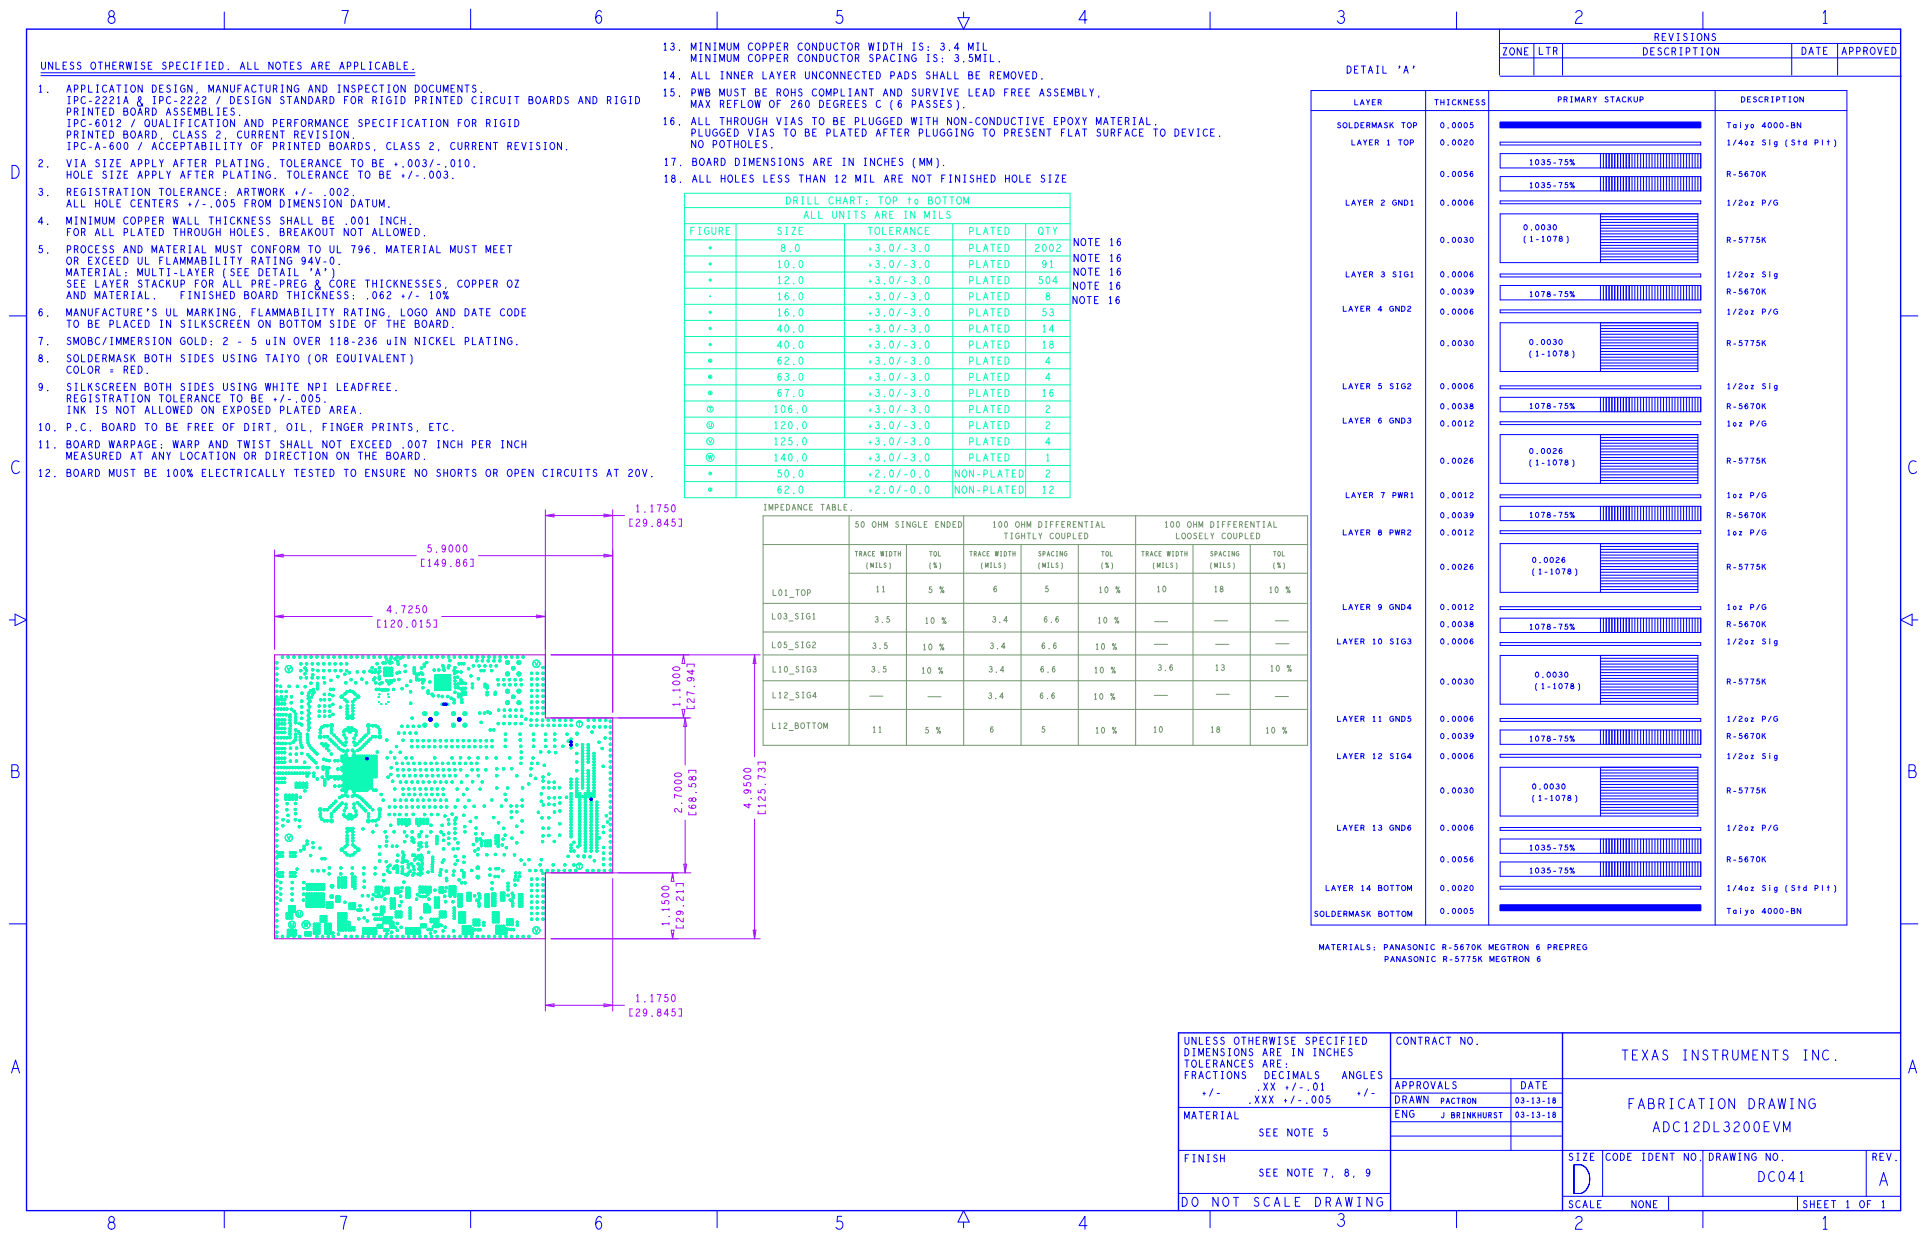
[picture p43: page 21]

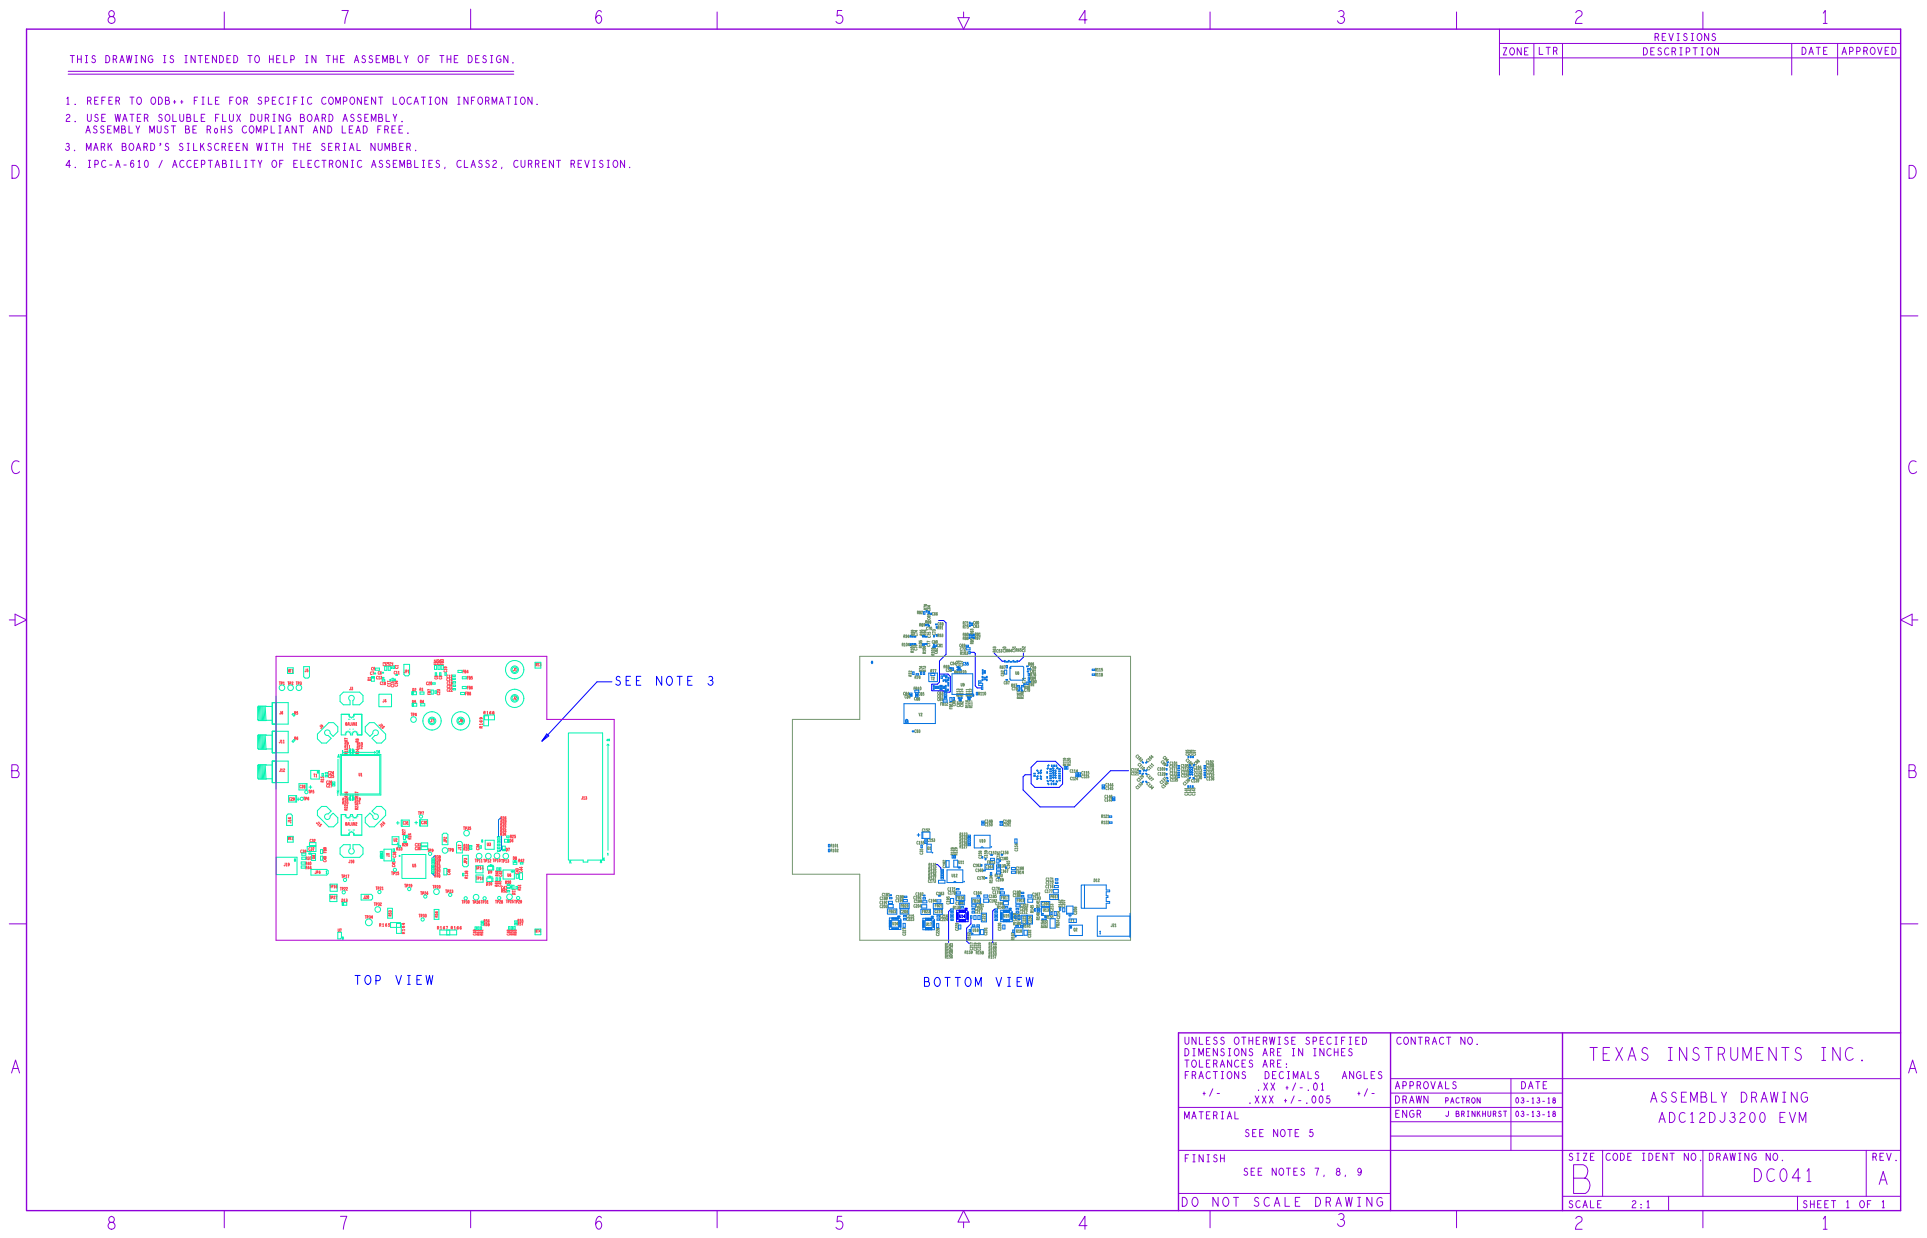
[picture p44: page 22]
