priimak/HaasoscopePro/adc board/haasoscope_pro_adc_board - no blind.brd

## EAGLE design adc board/haasoscope_pro_adc_board - no blind.brd (2024-07-29)

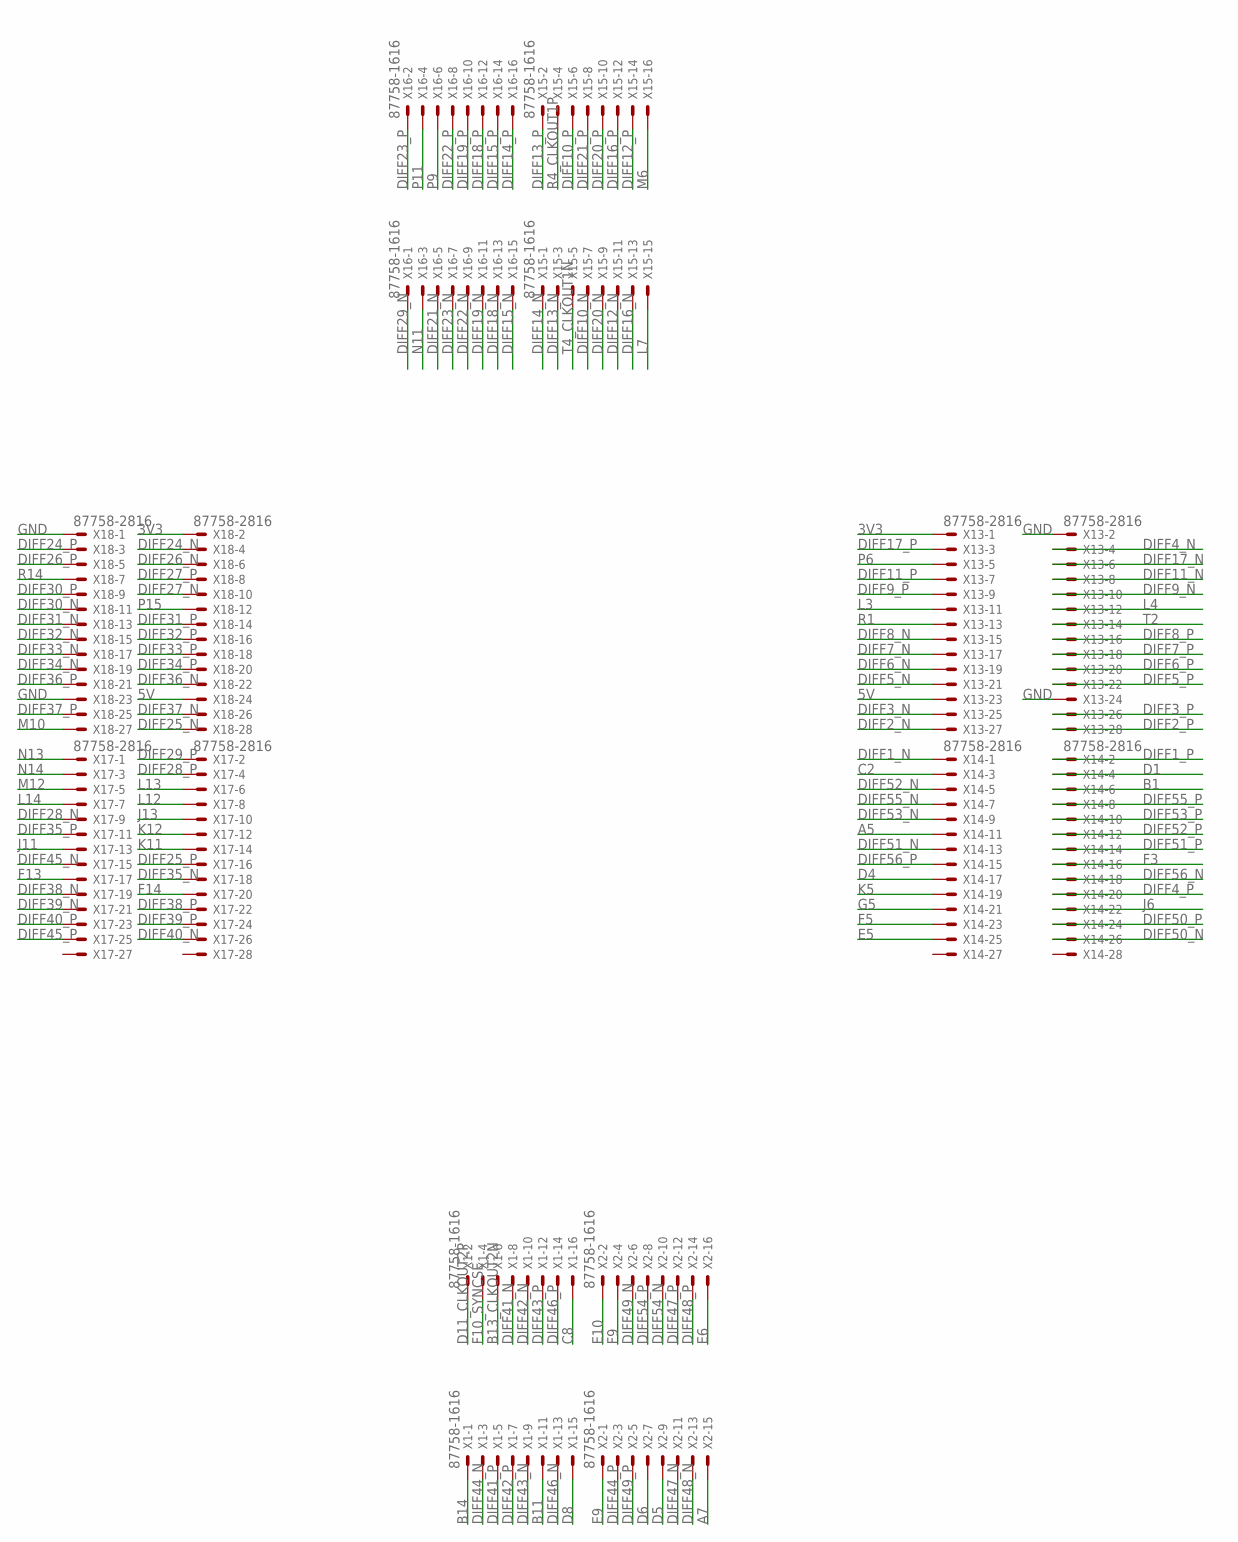
[picture p90: schematic haasoscope_pro_adc_board - no blind.sch, sheet 1]

Parts:
X1, X2, X15, X16: 87758-1616
X13, X14, X17, X18: 87758-2816

Connections:
3V3: X13.1, X18.2; also elsewhere on the board
5V: X13.23, X18.24; also elsewhere on the board
A5: X14.11; also elsewhere on the board
A7: X2.15; also elsewhere on the board
B1: X14.6; also elsewhere on the board
B11: X1.11; also elsewhere on the board
B13_CLKOUT2N: X1.6; also elsewhere on the board
B14: X1.1; also elsewhere on the board
C2: X14.3; also elsewhere on the board
C8: X1.16; also elsewhere on the board
D1: X14.4; also elsewhere on the board
D4: X14.17; also elsewhere on the board
D5: X2.9; also elsewhere on the board
D6: X2.7; also elsewhere on the board
D8: X1.15; also elsewhere on the board
D11_CLKOUT2P: X1.2; also elsewhere on the board
DIFF1_N: X14.1; also elsewhere on the board
DIFF1_P: X14.2; also elsewhere on the board
DIFF2_N: X13.27; also elsewhere on the board
DIFF2_P: X13.28; also elsewhere on the board
DIFF3_N: X13.25; also elsewhere on the board
DIFF3_P: X13.26; also elsewhere on the board
DIFF4_N: X13.4; also elsewhere on the board
DIFF4_P: X14.20; also elsewhere on the board
DIFF5_N: X13.21; also elsewhere on the board
DIFF5_P: X13.22; also elsewhere on the board
DIFF6_N: X13.19; also elsewhere on the board
DIFF6_P: X13.20; also elsewhere on the board
DIFF7_N: X13.17; also elsewhere on the board
DIFF7_P: X13.18; also elsewhere on the board
DIFF8_N: X13.15; also elsewhere on the board
DIFF8_P: X13.16; also elsewhere on the board
DIFF9_N: X13.10; also elsewhere on the board
DIFF9_P: X13.9; also elsewhere on the board
DIFF10_N: X15.7; also elsewhere on the board
DIFF10_P: X15.6; also elsewhere on the board
DIFF11_N: X13.8; also elsewhere on the board
DIFF11_P: X13.7; also elsewhere on the board
DIFF12_N: X15.11; also elsewhere on the board
DIFF12_P: X15.14; also elsewhere on the board
DIFF13_N: X15.3; also elsewhere on the board
DIFF13_P: X15.2; also elsewhere on the board
DIFF14_N: X15.1; also elsewhere on the board
DIFF14_P: X16.16; also elsewhere on the board
DIFF15_N: X16.15; also elsewhere on the board
DIFF15_P: X16.14; also elsewhere on the board
DIFF16_N: X15.13; also elsewhere on the board
DIFF16_P: X15.12; also elsewhere on the board
DIFF17_N: X13.6; also elsewhere on the board
DIFF17_P: X13.3; also elsewhere on the board
DIFF18_N: X16.13; also elsewhere on the board
DIFF18_P: X16.12; also elsewhere on the board
DIFF19_N: X16.11; also elsewhere on the board
DIFF19_P: X16.10; also elsewhere on the board
DIFF20_N: X15.9; also elsewhere on the board
DIFF20_P: X15.10; also elsewhere on the board
DIFF21_N: X16.5; also elsewhere on the board
DIFF21_P: X15.8; also elsewhere on the board
DIFF22_N: X16.9; also elsewhere on the board
DIFF22_P: X16.8; also elsewhere on the board
DIFF23_N: X16.7; also elsewhere on the board
DIFF23_P: X16.2; also elsewhere on the board
DIFF24_N: X18.4; also elsewhere on the board
DIFF24_P: X18.3; also elsewhere on the board
DIFF25_N: X18.28; also elsewhere on the board
DIFF25_P: X17.16; also elsewhere on the board
DIFF26_N: X18.6; also elsewhere on the board
DIFF26_P: X18.5; also elsewhere on the board
DIFF27_N: X18.10; also elsewhere on the board
DIFF27_P: X18.8; also elsewhere on the board
DIFF28_N: X17.9; also elsewhere on the board
DIFF28_P: X17.4; also elsewhere on the board
DIFF29_N: X16.1; also elsewhere on the board
DIFF29_P: X17.2; also elsewhere on the board
DIFF30_N: X18.11; also elsewhere on the board
DIFF30_P: X18.9; also elsewhere on the board
DIFF31_N: X18.13; also elsewhere on the board
DIFF31_P: X18.14; also elsewhere on the board
DIFF32_N: X18.15; also elsewhere on the board
DIFF32_P: X18.16; also elsewhere on the board
DIFF33_N: X18.17; also elsewhere on the board
DIFF33_P: X18.18; also elsewhere on the board
DIFF34_N: X18.19; also elsewhere on the board
DIFF34_P: X18.20; also elsewhere on the board
DIFF35_N: X17.18; also elsewhere on the board
DIFF35_P: X17.11; also elsewhere on the board
DIFF36_N: X18.22; also elsewhere on the board
DIFF36_P: X18.21; also elsewhere on the board
DIFF37_N: X18.26; also elsewhere on the board
DIFF37_P: X18.25; also elsewhere on the board
DIFF38_N: X17.19; also elsewhere on the board
DIFF38_P: X17.22; also elsewhere on the board
DIFF39_N: X17.21; also elsewhere on the board
DIFF39_P: X17.24; also elsewhere on the board
DIFF40_N: X17.26; also elsewhere on the board
DIFF40_P: X17.23; also elsewhere on the board
DIFF41_N: X1.8; also elsewhere on the board
DIFF41_P: X1.5; also elsewhere on the board
DIFF42_N: X1.10; also elsewhere on the board
DIFF42_P: X1.7; also elsewhere on the board
DIFF43_N: X1.9; also elsewhere on the board
DIFF43_P: X1.12; also elsewhere on the board
DIFF44_N: X1.3; also elsewhere on the board
DIFF44_P: X2.3; also elsewhere on the board
DIFF45_N: X17.15; also elsewhere on the board
DIFF45_P: X17.25; also elsewhere on the board
DIFF46_N: X1.13; also elsewhere on the board
DIFF46_P: X1.14; also elsewhere on the board
DIFF47_N: X2.11; also elsewhere on the board
DIFF47_P: X2.12; also elsewhere on the board
DIFF48_N: X2.13; also elsewhere on the board
DIFF48_P: X2.14; also elsewhere on the board
DIFF49_N: X2.6; also elsewhere on the board
DIFF49_P: X2.5; also elsewhere on the board
DIFF50_N: X14.26; also elsewhere on the board
DIFF50_P: X14.24; also elsewhere on the board
DIFF51_N: X14.13; also elsewhere on the board
DIFF51_P: X14.14; also elsewhere on the board
DIFF52_N: X14.5; also elsewhere on the board
DIFF52_P: X14.12; also elsewhere on the board
DIFF53_N: X14.9; also elsewhere on the board
DIFF53_P: X14.10; also elsewhere on the board
DIFF54_N: X2.10; also elsewhere on the board
DIFF54_P: X2.8; also elsewhere on the board
DIFF55_N: X14.7; also elsewhere on the board
DIFF55_P: X14.8; also elsewhere on the board
DIFF56_N: X14.18; also elsewhere on the board
DIFF56_P: X14.15; also elsewhere on the board
E5: X14.25; also elsewhere on the board
E6: X2.16; also elsewhere on the board
E9: X2.1; also elsewhere on the board
E10: X2.2; also elsewhere on the board
F3: X14.16; also elsewhere on the board
F5: X14.23; also elsewhere on the board
F9: X2.4; also elsewhere on the board
F10_SYNCSE: X1.4; also elsewhere on the board
F13: X17.17; also elsewhere on the board
F14: X17.20; also elsewhere on the board
G5: X14.21; also elsewhere on the board
GND: X13.2, X13.24, X18.1, X18.23; also elsewhere on the board
J6: X14.22; also elsewhere on the board
J11: X17.13; also elsewhere on the board
J13: X17.10; also elsewhere on the board
K5: X14.19; also elsewhere on the board
K11: X17.14; also elsewhere on the board
K12: X17.12; also elsewhere on the board
L3: X13.11; also elsewhere on the board
L4: X13.12; also elsewhere on the board
L7: X15.15; also elsewhere on the board
L12: X17.8; also elsewhere on the board
L13: X17.6; also elsewhere on the board
L14: X17.7; also elsewhere on the board
M6: X15.16; also elsewhere on the board
M10: X18.27; also elsewhere on the board
M12: X17.5; also elsewhere on the board
N11: X16.3; also elsewhere on the board
N13: X17.1; also elsewhere on the board
N14: X17.3; also elsewhere on the board
P6: X13.5; also elsewhere on the board
P9: X16.6; also elsewhere on the board
P11: X16.4; also elsewhere on the board
P15: X18.12; also elsewhere on the board
R1: X13.13; also elsewhere on the board
R4_CLKOUT1P: X15.4; also elsewhere on the board
R14: X18.7; also elsewhere on the board
T2: X13.14; also elsewhere on the board
T4_CLKOUT1N: X15.5; also elsewhere on the board
