priimak/HaasoscopePro/adc board/haasoscope_pro_adc_board - no blind.brd

## EAGLE design adc board/haasoscope_pro_adc_board - no blind.brd (continued)

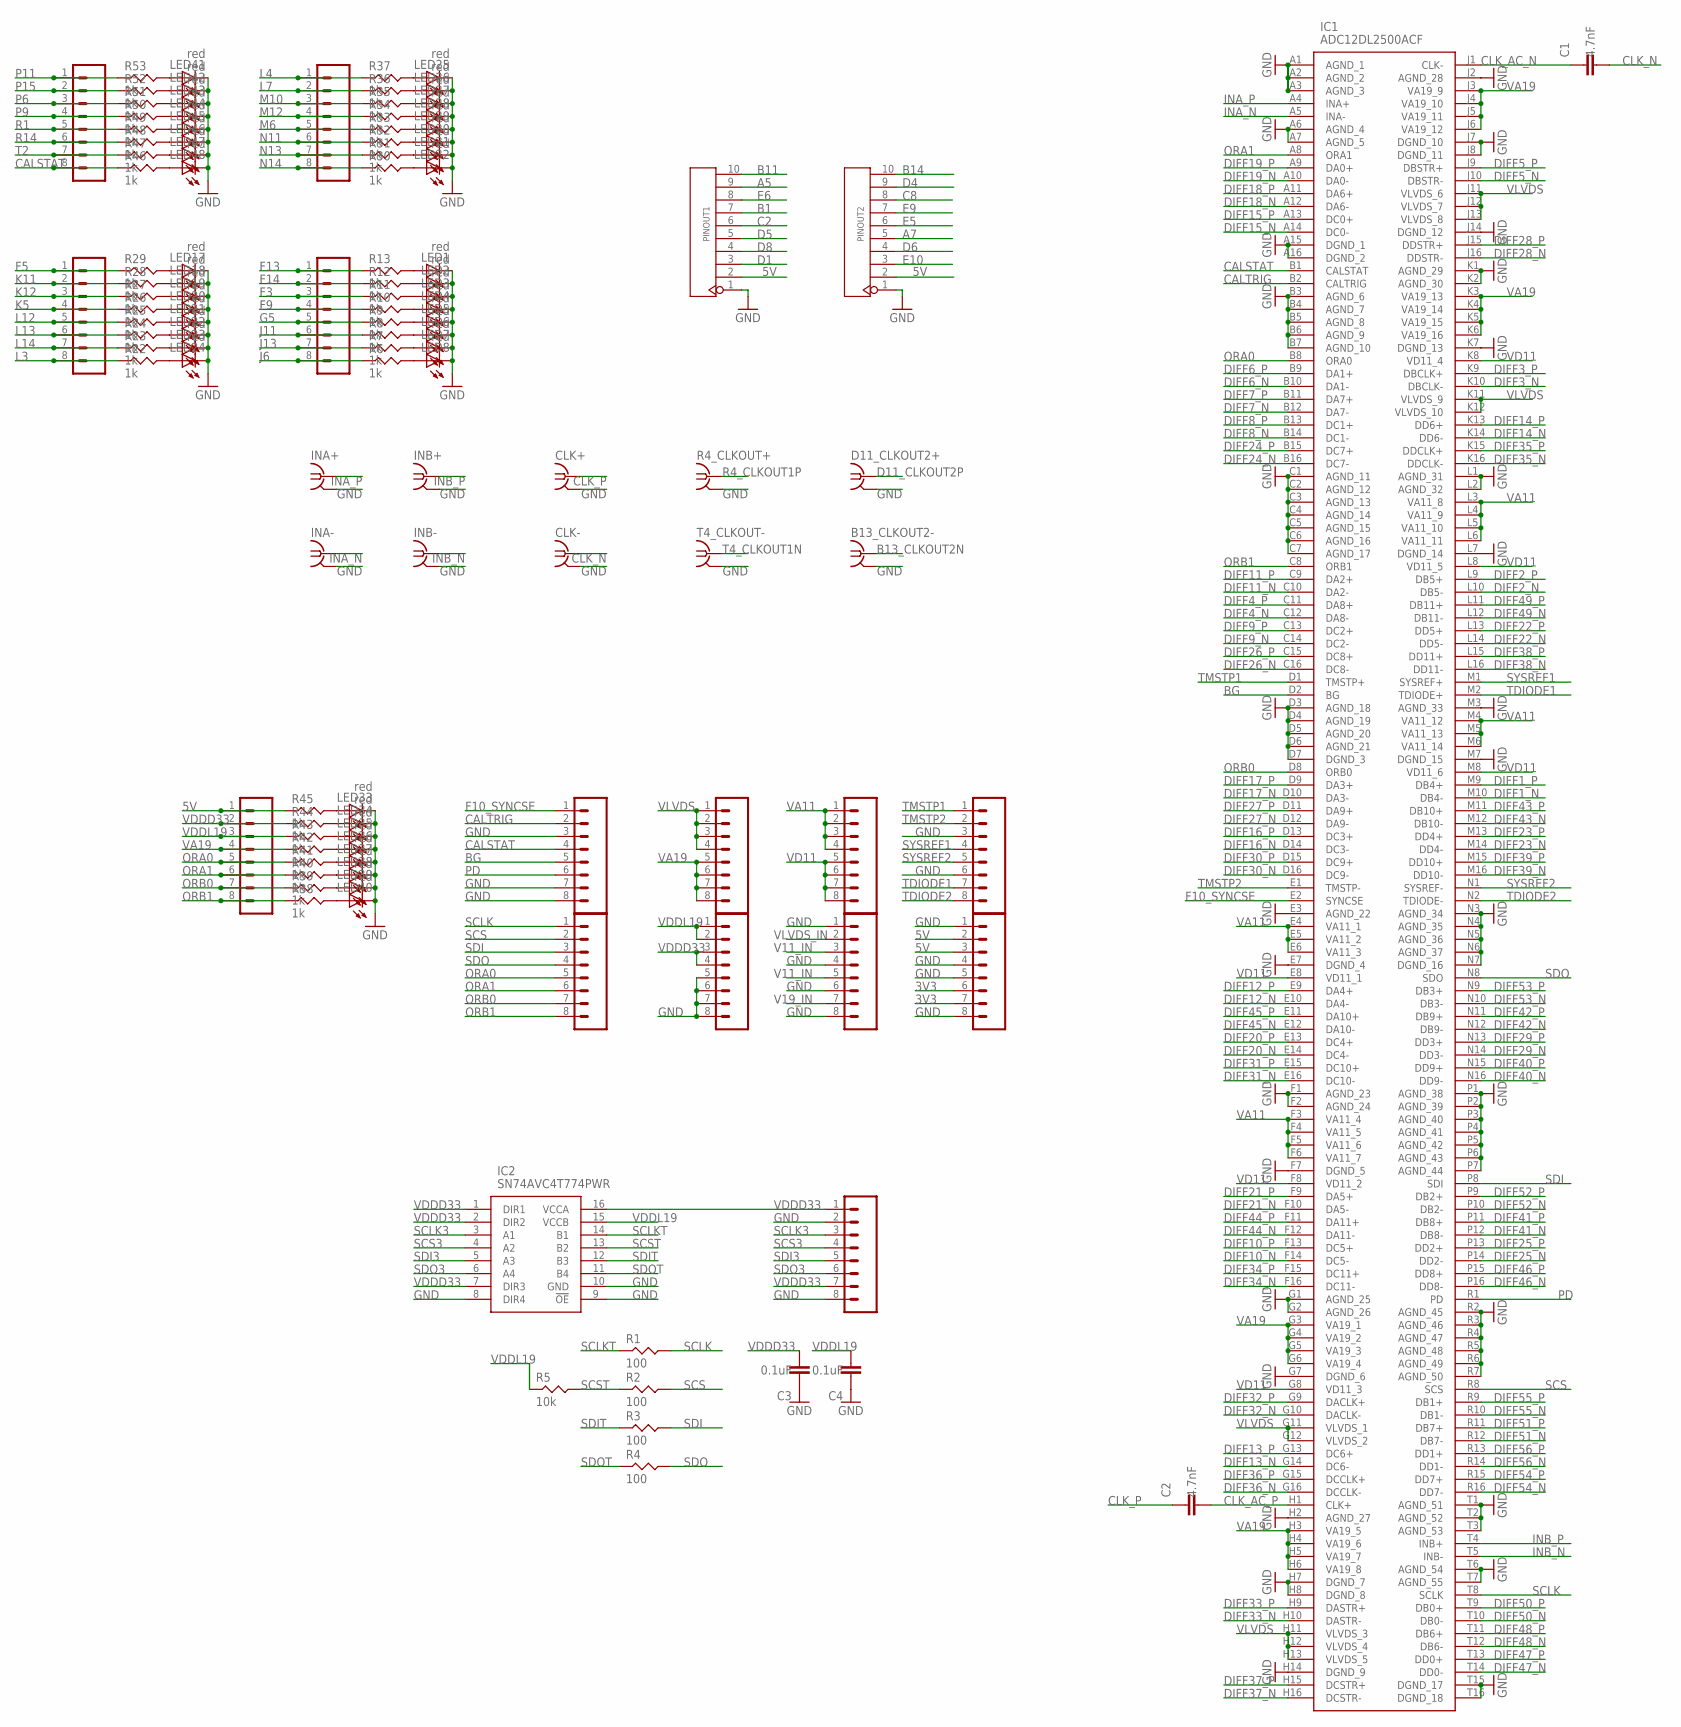
[picture p91: schematic haasoscope_pro_adc_board - no blind.sch, sheet 2]

Parts:
B13_CLKOUT2-: BU-SMB-V
C1, C2: 4.7nF; RESC0402_N
C3, C4: 0.1uF; RESC0402_N
CLK+: BU-SMB-V
CLK-: BU-SMB-V
D11_CLKOUT2+: BU-SMB-V
IC1: ADC12DL2500ACF; BGA256C100P16X16_1700X1700X331; MANUFACTURER_PART_NUMBER ADC12DL500ACF
IC2: SN74AVC4T774PWR; SOP65P640X120-16N
INA+: BU-SMB-V
INA-: BU-SMB-V
INB+: BU-SMB-V
INB-: BU-SMB-V
J1, J2, J3, J4, J5, J6, J7, J8, J10, J11, J12, J13, J16, J17: 8pin; 1X08
LED1, LED2, LED3, LED4, LED5, LED6, LED7, LED8, LED17, LED18, LED19, LED20, LED21, LED22, LED23, LED24, LED25, LED26, LED27, LED28, LED29, LED30, LED31, LED32, LED33, LED34, LED35, LED36, LED37, LED38, LED39, LED40, LED41, LED42, LED43, LED44, LED45, LED46, LED47, LED48: red; CHIP-LED0603
PINOUT1, PINOUT2: YELLOW-10P-2.54; H10-2.54
R1, R2, R3, R4: 100; RES-0402
R4_CLKOUT+: BU-SMB-V
R5: 10k; RES-0402
R6, R7, R8, R9, R10, R11, R12, R13, R22, R23, R24, R25, R26, R27, R28, R29, R30, R31, R32, R33, R34, R35, R36, R37, R38, R39, R40, R41, R42, R43, R44, R45, R46, R47, R48, R49, R50, R51, R52, R53: 1k; RES-0402
T4_CLKOUT-: BU-SMB-V

Connections:
3V3: J6.6, J6.7; also elsewhere on the board
5V: J6.2, J6.3, J12.1, PINOUT1.2, PINOUT2.2, R45.P$1; also elsewhere on the board
A5: PINOUT1.9; also elsewhere on the board
A7: PINOUT2.5; also elsewhere on the board
B1: PINOUT1.7; also elsewhere on the board
B11: PINOUT1.10; also elsewhere on the board
B13_CLKOUT2N: B13_CLKOUT2-.1; also elsewhere on the board
B14: PINOUT2.10; also elsewhere on the board
BG: IC1.D2 (BG), J17.5
C2: PINOUT1.6; also elsewhere on the board
C8: PINOUT2.8; also elsewhere on the board
CALSTAT: IC1.B1 (CALSTAT), J13.8, J17.4, R46.P$1
CALTRIG: IC1.B2 (CALTRIG), J17.2
CLK_AC_N: C1.1, IC1.J1 (CLK-)
CLK_AC_P: C2.2, IC1.H1 (CLK+)
CLK_N: C1.2, CLK-.1
CLK_P: C2.1, CLK+.1
D1: PINOUT1.3; also elsewhere on the board
D4: PINOUT2.9; also elsewhere on the board
D5: PINOUT1.5; also elsewhere on the board
D6: PINOUT2.4; also elsewhere on the board
D8: PINOUT1.4; also elsewhere on the board
D11_CLKOUT2P: D11_CLKOUT2+.1; also elsewhere on the board
DIFF1_N: IC1.M10 (DB4-); also elsewhere on the board
DIFF1_P: IC1.M9 (DB4+); also elsewhere on the board
DIFF2_N: IC1.L10 (DB5-); also elsewhere on the board
DIFF2_P: IC1.L9 (DB5+); also elsewhere on the board
DIFF3_N: IC1.K10 (DBCLK-); also elsewhere on the board
DIFF3_P: IC1.K9 (DBCLK+); also elsewhere on the board
DIFF4_N: IC1.C12 (DA8-); also elsewhere on the board
DIFF4_P: IC1.C11 (DA8+); also elsewhere on the board
DIFF5_N: IC1.J10 (DBSTR-); also elsewhere on the board
DIFF5_P: IC1.J9 (DBSTR+); also elsewhere on the board
DIFF6_N: IC1.B10 (DA1-); also elsewhere on the board
DIFF6_P: IC1.B9 (DA1+); also elsewhere on the board
DIFF7_N: IC1.B12 (DA7-); also elsewhere on the board
DIFF7_P: IC1.B11 (DA7+); also elsewhere on the board
DIFF8_N: IC1.B14 (DC1-); also elsewhere on the board
DIFF8_P: IC1.B13 (DC1+); also elsewhere on the board
DIFF9_N: IC1.C14 (DC2-); also elsewhere on the board
DIFF9_P: IC1.C13 (DC2+); also elsewhere on the board
DIFF10_N: IC1.F14 (DC5-); also elsewhere on the board
DIFF10_P: IC1.F13 (DC5+); also elsewhere on the board
DIFF11_N: IC1.C10 (DA2-); also elsewhere on the board
DIFF11_P: IC1.C9 (DA2+); also elsewhere on the board
DIFF12_N: IC1.E10 (DA4-); also elsewhere on the board
DIFF12_P: IC1.E9 (DA4+); also elsewhere on the board
DIFF13_N: IC1.G14 (DC6-); also elsewhere on the board
DIFF13_P: IC1.G13 (DC6+); also elsewhere on the board
DIFF14_N: IC1.K14 (DD6-); also elsewhere on the board
DIFF14_P: IC1.K13 (DD6+); also elsewhere on the board
DIFF15_N: IC1.A14 (DC0-); also elsewhere on the board
DIFF15_P: IC1.A13 (DC0+); also elsewhere on the board
DIFF16_N: IC1.D14 (DC3-); also elsewhere on the board
DIFF16_P: IC1.D13 (DC3+); also elsewhere on the board
DIFF17_N: IC1.D10 (DA3-); also elsewhere on the board
DIFF17_P: IC1.D9 (DA3+); also elsewhere on the board
DIFF18_N: IC1.A12 (DA6-); also elsewhere on the board
DIFF18_P: IC1.A11 (DA6+); also elsewhere on the board
DIFF19_N: IC1.A10 (DA0-); also elsewhere on the board
DIFF19_P: IC1.A9 (DA0+); also elsewhere on the board
DIFF20_N: IC1.E14 (DC4-); also elsewhere on the board
DIFF20_P: IC1.E13 (DC4+); also elsewhere on the board
DIFF21_N: IC1.F10 (DA5-); also elsewhere on the board
DIFF21_P: IC1.F9 (DA5+); also elsewhere on the board
DIFF22_N: IC1.L14 (DD5-); also elsewhere on the board
DIFF22_P: IC1.L13 (DD5+); also elsewhere on the board
DIFF23_N: IC1.M14 (DD4-); also elsewhere on the board
DIFF23_P: IC1.M13 (DD4+); also elsewhere on the board
DIFF24_N: IC1.B16 (DC7-); also elsewhere on the board
DIFF24_P: IC1.B15 (DC7+); also elsewhere on the board
DIFF25_N: IC1.P14 (DD2-); also elsewhere on the board
DIFF25_P: IC1.P13 (DD2+); also elsewhere on the board
DIFF26_N: IC1.C16 (DC8-); also elsewhere on the board
DIFF26_P: IC1.C15 (DC8+); also elsewhere on the board
DIFF27_N: IC1.D12 (DA9-); also elsewhere on the board
DIFF27_P: IC1.D11 (DA9+); also elsewhere on the board
DIFF28_N: IC1.J16 (DDSTR-); also elsewhere on the board
DIFF28_P: IC1.J15 (DDSTR+); also elsewhere on the board
DIFF29_N: IC1.N14 (DD3-); also elsewhere on the board
DIFF29_P: IC1.N13 (DD3+); also elsewhere on the board
DIFF30_N: IC1.D16 (DC9-); also elsewhere on the board
DIFF30_P: IC1.D15 (DC9+); also elsewhere on the board
DIFF31_N: IC1.E16 (DC10-); also elsewhere on the board
DIFF31_P: IC1.E15 (DC10+); also elsewhere on the board
DIFF32_N: IC1.G10 (DACLK-); also elsewhere on the board
DIFF32_P: IC1.G9 (DACLK+); also elsewhere on the board
DIFF33_N: IC1.H10 (DASTR-); also elsewhere on the board
DIFF33_P: IC1.H9 (DASTR+); also elsewhere on the board
DIFF34_N: IC1.F16 (DC11-); also elsewhere on the board
DIFF34_P: IC1.F15 (DC11+); also elsewhere on the board
DIFF35_N: IC1.K16 (DDCLK-); also elsewhere on the board
DIFF35_P: IC1.K15 (DDCLK+); also elsewhere on the board
DIFF36_N: IC1.G16 (DCCLK-); also elsewhere on the board
DIFF36_P: IC1.G15 (DCCLK+); also elsewhere on the board
DIFF37_N: IC1.H16 (DCSTR-); also elsewhere on the board
DIFF37_P: IC1.H15 (DCSTR+); also elsewhere on the board
DIFF38_N: IC1.L16 (DD11-); also elsewhere on the board
DIFF38_P: IC1.L15 (DD11+); also elsewhere on the board
DIFF39_N: IC1.M16 (DD10-); also elsewhere on the board
DIFF39_P: IC1.M15 (DD10+); also elsewhere on the board
DIFF40_N: IC1.N16 (DD9-); also elsewhere on the board
DIFF40_P: IC1.N15 (DD9+); also elsewhere on the board
DIFF41_N: IC1.P12 (DB8-); also elsewhere on the board
DIFF41_P: IC1.P11 (DB8+); also elsewhere on the board
DIFF42_N: IC1.N12 (DB9-); also elsewhere on the board
DIFF42_P: IC1.N11 (DB9+); also elsewhere on the board
DIFF43_N: IC1.M12 (DB10-); also elsewhere on the board
DIFF43_P: IC1.M11 (DB10+); also elsewhere on the board
DIFF44_N: IC1.F12 (DA11-); also elsewhere on the board
DIFF44_P: IC1.F11 (DA11+); also elsewhere on the board
DIFF45_N: IC1.E12 (DA10-); also elsewhere on the board
DIFF45_P: IC1.E11 (DA10+); also elsewhere on the board
DIFF46_N: IC1.P16 (DD8-); also elsewhere on the board
DIFF46_P: IC1.P15 (DD8+); also elsewhere on the board
DIFF47_N: IC1.T14 (DD0-); also elsewhere on the board
DIFF47_P: IC1.T13 (DD0+); also elsewhere on the board
DIFF48_N: IC1.T12 (DB6-); also elsewhere on the board
DIFF48_P: IC1.T11 (DB6+); also elsewhere on the board
DIFF49_N: IC1.L12 (DB11-); also elsewhere on the board
DIFF49_P: IC1.L11 (DB11+); also elsewhere on the board
DIFF50_N: IC1.T10 (DB0-); also elsewhere on the board
DIFF50_P: IC1.T9 (DB0+); also elsewhere on the board
DIFF51_N: IC1.R12 (DB7-); also elsewhere on the board
DIFF51_P: IC1.R11 (DB7+); also elsewhere on the board
DIFF52_N: IC1.P10 (DB2-); also elsewhere on the board
DIFF52_P: IC1.P9 (DB2+); also elsewhere on the board
DIFF53_N: IC1.N10 (DB3-); also elsewhere on the board
DIFF53_P: IC1.N9 (DB3+); also elsewhere on the board
DIFF54_N: IC1.R16 (DD7-); also elsewhere on the board
DIFF54_P: IC1.R15 (DD7+); also elsewhere on the board
DIFF55_N: IC1.R10 (DB1-); also elsewhere on the board
DIFF55_P: IC1.R9 (DB1+); also elsewhere on the board
DIFF56_N: IC1.R14 (DD1-); also elsewhere on the board
DIFF56_P: IC1.R13 (DD1+); also elsewhere on the board
E5: PINOUT2.6; also elsewhere on the board
E6: PINOUT1.8; also elsewhere on the board
E9: PINOUT2.7; also elsewhere on the board
E10: PINOUT2.3; also elsewhere on the board
F3: J8.3, R11.P$1; also elsewhere on the board
F5: J10.1, R29.P$1; also elsewhere on the board
F9: J8.4, R10.P$1; also elsewhere on the board
F10_SYNCSE: IC1.E2 (SYNCSE), J17.1; also elsewhere on the board
F13: J8.1, R13.P$1; also elsewhere on the board
F14: J8.2, R12.P$1; also elsewhere on the board
G5: J8.5, R9.P$1; also elsewhere on the board
GND: B13_CLKOUT2-.2, B13_CLKOUT2-.3 (2), B13_CLKOUT2-.4 (2), B13_CLKOUT2-.5 (2), C3.1, C4.1, CLK+.2, CLK+.3 (2), CLK+.4 (2), CLK+.5 (2), CLK-.2, CLK-.3 (2), CLK-.4 (2), CLK-.5 (2), D11_CLKOUT2+.2, D11_CLKOUT2+.3 (2), D11_CLKOUT2+.4 (2), D11_CLKOUT2+.5 (2), IC1.A1 (AGND_1), IC1.A2 (AGND_2), IC1.A3 (AGND_3), IC1.A6 (AGND_4), IC1.A7 (AGND_5), IC1.A15 (DGND_1), IC1.A16 (DGND_2), IC1.B3 (AGND_6), IC1.B4 (AGND_7), IC1.B5 (AGND_8), IC1.B6 (AGND_9), IC1.B7 (AGND_10), IC1.C1 (AGND_11), IC1.C2 (AGND_12), IC1.C3 (AGND_13), IC1.C4 (AGND_14), IC1.C5 (AGND_15), IC1.C6 (AGND_16), IC1.C7 (AGND_17), IC1.D3 (AGND_18), IC1.D4 (AGND_19), IC1.D5 (AGND_20), IC1.D6 (AGND_21), IC1.D7 (DGND_3), IC1.E3 (AGND_22), IC1.E7 (DGND_4), IC1.F1 (AGND_23), IC1.F2 (AGND_24), IC1.F7 (DGND_5), IC1.G1 (AGND_25), IC1.G2 (AGND_26), IC1.G7 (DGND_6), IC1.H2 (AGND_27), IC1.H7 (DGND_7), IC1.H8 (DGND_8), IC1.H14 (DGND_9), IC1.J2 (AGND_28), IC1.J7 (DGND_10), IC1.J8 (DGND_11), IC1.J14 (DGND_12), IC1.K1 (AGND_29), IC1.K2 (AGND_30), IC1.K7 (DGND_13), IC1.L1 (AGND_31), IC1.L2 (AGND_32), IC1.L7 (DGND_14), IC1.M3 (AGND_33), IC1.M7 (DGND_15), IC1.N3 (AGND_34), IC1.N4 (AGND_35), IC1.N5 (AGND_36), IC1.N6 (AGND_37), IC1.N7 (DGND_16), IC1.P1 (AGND_38), IC1.P2 (AGND_39), IC1.P3 (AGND_40), IC1.P4 (AGND_41), IC1.P5 (AGND_42), IC1.P6 (AGND_43), IC1.P7 (AGND_44), IC1.R2 (AGND_45), IC1.R3 (AGND_46), IC1.R4 (AGND_47), IC1.R5 (AGND_48), IC1.R6 (AGND_49), IC1.R7 (AGND_50), IC1.T1 (AGND_51), IC1.T2 (AGND_52), IC1.T3 (AGND_53), IC1.T6 (AGND_54), IC1.T7 (AGND_55), IC1.T15 (DGND_17), IC1.T16 (DGND_18), IC2.8 (DIR4), IC2.9 (!OE), IC2.10 (GND), INA+.2, INA+.3 (2), INA+.4 (2), INA+.5 (2), INA-.2, INA-.3 (2), INA-.4 (2), INA-.5 (2), INB+.2, INB+.3 (2), INB+.4 (2), INB+.5 (2), INB-.2, INB-.3 (2), INB-.4 (2), INB-.5 (2), J2.5, J2.6, J2.7, J2.8, J4.2, J4.8, J5.1, J5.4, J5.6, J5.8, J6.1, J6.4, J6.5, J6.8, J7.3, J7.6, J17.3, J17.7, J17.8, LED1.C, LED2.C, LED3.C, LED4.C, LED5.C, LED6.C, LED7.C, LED8.C, LED17.C, LED18.C, LED19.C, LED20.C, LED21.C, LED22.C, LED23.C, LED24.C, LED25.C, LED26.C, LED27.C, LED28.C, LED29.C, LED30.C, LED31.C, LED32.C, LED33.C, LED34.C, LED35.C, LED36.C, LED37.C, LED38.C, LED39.C, LED40.C, LED41.C, LED42.C, LED43.C, LED44.C, LED45.C, LED46.C, LED47.C, LED48.C, PINOUT1.1, PINOUT2.1, R4_CLKOUT+.2, R4_CLKOUT+.3 (2), R4_CLKOUT+.4 (2), R4_CLKOUT+.5 (2), T4_CLKOUT-.2, T4_CLKOUT-.3 (2), T4_CLKOUT-.4 (2), T4_CLKOUT-.5 (2); also elsewhere on the board
INA_N: IC1.A5 (INA-), INA-.1
INA_P: IC1.A4 (INA+), INA+.1
INB_N: IC1.T5 (INB-), INB-.1
INB_P: IC1.T4 (INB+), INB+.1
J6: J8.8, R6.P$1; also elsewhere on the board
J11: J8.6, R8.P$1; also elsewhere on the board
J13: J8.7, R7.P$1; also elsewhere on the board
K5: J10.4, R26.P$1; also elsewhere on the board
K11: J10.2, R28.P$1; also elsewhere on the board
K12: J10.3, R27.P$1; also elsewhere on the board
L3: J10.8, R22.P$1; also elsewhere on the board
L4: J11.1, R37.P$1; also elsewhere on the board
L7: J11.2, R36.P$1; also elsewhere on the board
L12: J10.5, R25.P$1; also elsewhere on the board
L13: J10.6, R24.P$1; also elsewhere on the board
L14: J10.7, R23.P$1; also elsewhere on the board
M6: J11.5, R33.P$1; also elsewhere on the board
M10: J11.3, R35.P$1; also elsewhere on the board
M12: J11.4, R34.P$1; also elsewhere on the board
N11: J11.6, R32.P$1; also elsewhere on the board
N13: J11.7, R31.P$1; also elsewhere on the board
N14: J11.8, R30.P$1; also elsewhere on the board
unnamed: LED1.A, R13.P$2
unnamed: LED2.A, R12.P$2
unnamed: LED3.A, R11.P$2
unnamed: LED4.A, R10.P$2
unnamed: LED5.A, R9.P$2
unnamed: LED6.A, R8.P$2
unnamed: LED7.A, R7.P$2
unnamed: LED8.A, R6.P$2
unnamed: LED17.A, R29.P$2
unnamed: LED18.A, R28.P$2
unnamed: LED19.A, R27.P$2
unnamed: LED20.A, R26.P$2
unnamed: LED21.A, R25.P$2
unnamed: LED22.A, R24.P$2
unnamed: LED23.A, R23.P$2
unnamed: LED24.A, R22.P$2
unnamed: LED25.A, R37.P$2
unnamed: LED26.A, R36.P$2
unnamed: LED27.A, R35.P$2
unnamed: LED28.A, R34.P$2
unnamed: LED29.A, R33.P$2
unnamed: LED30.A, R32.P$2
unnamed: LED31.A, R31.P$2
unnamed: LED32.A, R30.P$2
unnamed: LED33.A, R45.P$2
unnamed: LED34.A, R44.P$2
unnamed: LED35.A, R43.P$2
unnamed: LED36.A, R42.P$2
unnamed: LED37.A, R41.P$2
unnamed: LED38.A, R40.P$2
unnamed: LED39.A, R39.P$2
unnamed: LED40.A, R38.P$2
unnamed: LED41.A, R53.P$2
unnamed: LED42.A, R52.P$2
unnamed: LED43.A, R51.P$2
unnamed: LED44.A, R50.P$2
unnamed: LED45.A, R49.P$2
unnamed: LED46.A, R48.P$2
unnamed: LED47.A, R47.P$2
unnamed: LED48.A, R46.P$2
ORA0: IC1.B8 (ORA0), J12.5, J16.5, R41.P$1
ORA1: IC1.A8 (ORA1), J12.6, J16.6, R40.P$1
ORB0: IC1.D8 (ORB0), J12.7, J16.7, R39.P$1
ORB1: IC1.C8 (ORB1), J12.8, J16.8, R38.P$1
P6: J13.3, R51.P$1; also elsewhere on the board
P9: J13.4, R50.P$1; also elsewhere on the board
P11: J13.1, R53.P$1; also elsewhere on the board
P15: J13.2, R52.P$1; also elsewhere on the board
PD: IC1.R1 (PD), J17.6
R1: J13.5, R49.P$1; also elsewhere on the board
R4_CLKOUT1P: R4_CLKOUT+.1; also elsewhere on the board
R14: J13.6, R48.P$1; also elsewhere on the board
SCLK: IC1.T8 (SCLK), J16.1, R1.P$2
SCLK3: IC2.3 (A1), J4.3
SCLKT: IC2.14 (B1), R1.P$1
SCS: IC1.R8 (SCS), J16.2, R2.P$2
SCS3: IC2.4 (A2), J4.4
SCST: IC2.13 (B2), R2.P$1, R5.P$2
SDI: IC1.P8 (SDI), J16.3, R3.P$2
SDI3: IC2.5 (A3), J4.5
SDIT: IC2.12 (B3), R3.P$1
SDO: IC1.N8 (SDO), J16.4, R4.P$2
SDO3: IC2.6 (A4), J4.6
SDOT: IC2.11 (B4), R4.P$1
SYSREF1: IC1.M1 (SYSREF+), J7.4
SYSREF2: IC1.N1 (SYSREF-), J7.5
T2: J13.7, R47.P$1; also elsewhere on the board
T4_CLKOUT1N: T4_CLKOUT-.1; also elsewhere on the board
TDIODE1: IC1.M2 (TDIODE+), J7.7
TDIODE2: IC1.N2 (TDIODE-), J7.8
TMSTP1: IC1.D1 (TMSTP+), J7.1
TMSTP2: IC1.E1 (TMSTP-), J7.2
V11_IN: J5.3, J5.5; also elsewhere on the board
V19_IN: J5.7; also elsewhere on the board
VA11: IC1.E4 (VA11_1), IC1.E5 (VA11_2), IC1.E6 (VA11_3), IC1.F3 (VA11_4), IC1.F4 (VA11_5), IC1.F5 (VA11_6), IC1.F6 (VA11_7), IC1.L3 (VA11_8), IC1.L4 (VA11_9), IC1.L5 (VA11_10), IC1.L6 (VA11_11), IC1.M4 (VA11_12), IC1.M5 (VA11_13), IC1.M6 (VA11_14), J3.1, J3.2, J3.3, J3.4; also elsewhere on the board
VA19: IC1.G3 (VA19_1), IC1.G4 (VA19_2), IC1.G5 (VA19_3), IC1.G6 (VA19_4), IC1.H3 (VA19_5), IC1.H4 (VA19_6), IC1.H5 (VA19_7), IC1.H6 (VA19_8), IC1.J3 (VA19_9), IC1.J4 (VA19_10), IC1.J5 (VA19_11), IC1.J6 (VA19_12), IC1.K3 (VA19_13), IC1.K4 (VA19_14), IC1.K5 (VA19_15), IC1.K6 (VA19_16), J1.5, J1.6, J1.7, J1.8, J12.4, R42.P$1; also elsewhere on the board
VD11: IC1.E8 (VD11_1), IC1.F8 (VD11_2), IC1.G8 (VD11_3), IC1.K8 (VD11_4), IC1.L8 (VD11_5), IC1.M8 (VD11_6), J3.5, J3.6, J3.7, J3.8; also elsewhere on the board
VDDD33: C3.2, IC2.1 (DIR1), IC2.2 (DIR2), IC2.7 (DIR3), IC2.16 (VCCA), J2.3, J2.4, J4.1, J4.7, J12.2, R44.P$1
VDDL19: C4.2, IC2.15 (VCCB), J2.1, J2.2, J12.3, R5.P$1, R43.P$1; also elsewhere on the board
VLVDS: IC1.G11 (VLVDS_1), IC1.G12 (VLVDS_2), IC1.H11 (VLVDS_3), IC1.H12 (VLVDS_4), IC1.H13 (VLVDS_5), IC1.J11 (VLVDS_6), IC1.J12 (VLVDS_7), IC1.J13 (VLVDS_8), IC1.K11 (VLVDS_9), IC1.K12 (VLVDS_10), J1.1, J1.2, J1.3, J1.4; also elsewhere on the board
VLVDS_IN: J5.2; also elsewhere on the board

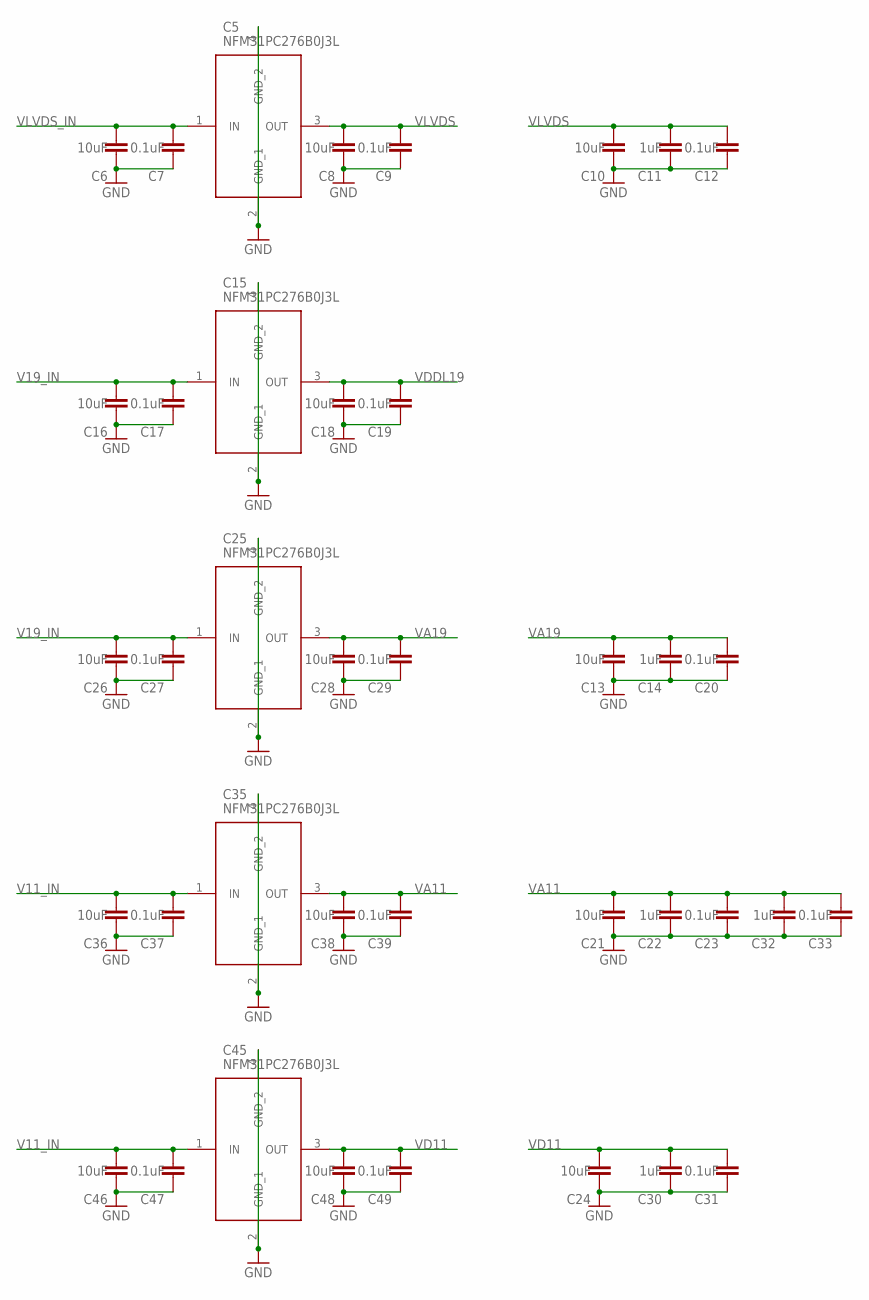
[picture p92: schematic haasoscope_pro_adc_board - no blind.sch, sheet 3]

Parts:
C5, C15, C25, C35, C45: NFM31PC276B0J3L; NFM31HK103R1H3L
C6, C8, C10, C13, C16, C18, C21, C24, C26, C28, C36, C38, C46, C48: 10uF; RESC0805_N
C7, C9, C12, C17, C19, C20, C23, C27, C29, C31, C33, C37, C39, C47, C49: 0.1uF; RESC0402_N
C11, C14, C22, C30, C32: 1uF; RESC0402_N

Connections:
GND: C5.2 (GND_1), C5.4 (GND_2), C6.1, C7.1, C8.1, C9.1, C10.1, C11.1, C12.1, C13.1, C14.1, C15.2 (GND_1), C15.4 (GND_2), C16.1, C17.1, C18.1, C19.1, C20.1, C21.1, C22.1, C23.1, C24.1, C25.2 (GND_1), C25.4 (GND_2), C26.1, C27.1, C28.1, C29.1, C30.1, C31.1, C32.1, C33.1, C35.2 (GND_1), C35.4 (GND_2), C36.1, C37.1, C38.1, C39.1, C45.2 (GND_1), C45.4 (GND_2), C46.1, C47.1, C48.1, C49.1; also elsewhere on the board
V11_IN: C35.1 (IN), C36.2, C37.2, C45.1 (IN), C46.2, C47.2; also elsewhere on the board
V19_IN: C15.1 (IN), C16.2, C17.2, C25.1 (IN), C26.2, C27.2; also elsewhere on the board
VA11: C21.2, C22.2, C23.2, C32.2, C33.2, C35.3 (OUT), C38.2, C39.2; also elsewhere on the board
VA19: C13.2, C14.2, C20.2, C25.3 (OUT), C28.2, C29.2; also elsewhere on the board
VD11: C24.2, C30.2, C31.2, C45.3 (OUT), C48.2, C49.2; also elsewhere on the board
VDDL19: C15.3 (OUT), C18.2, C19.2; also elsewhere on the board
VLVDS: C5.3 (OUT), C8.2, C9.2, C10.2, C11.2, C12.2; also elsewhere on the board
VLVDS_IN: C5.1 (IN), C6.2, C7.2; also elsewhere on the board

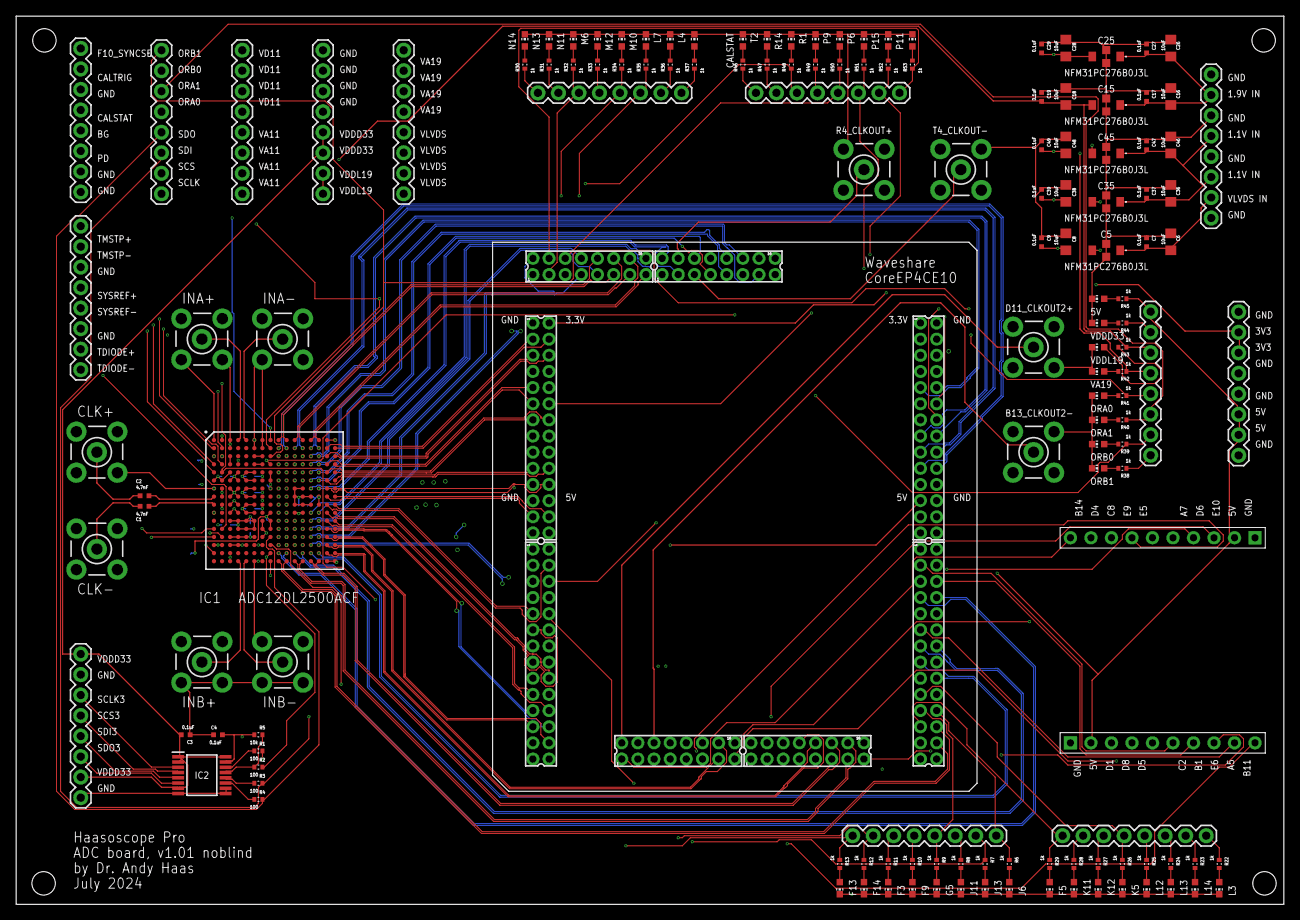
[picture p93: board haasoscope_pro_adc_board - no blind.brd from above]

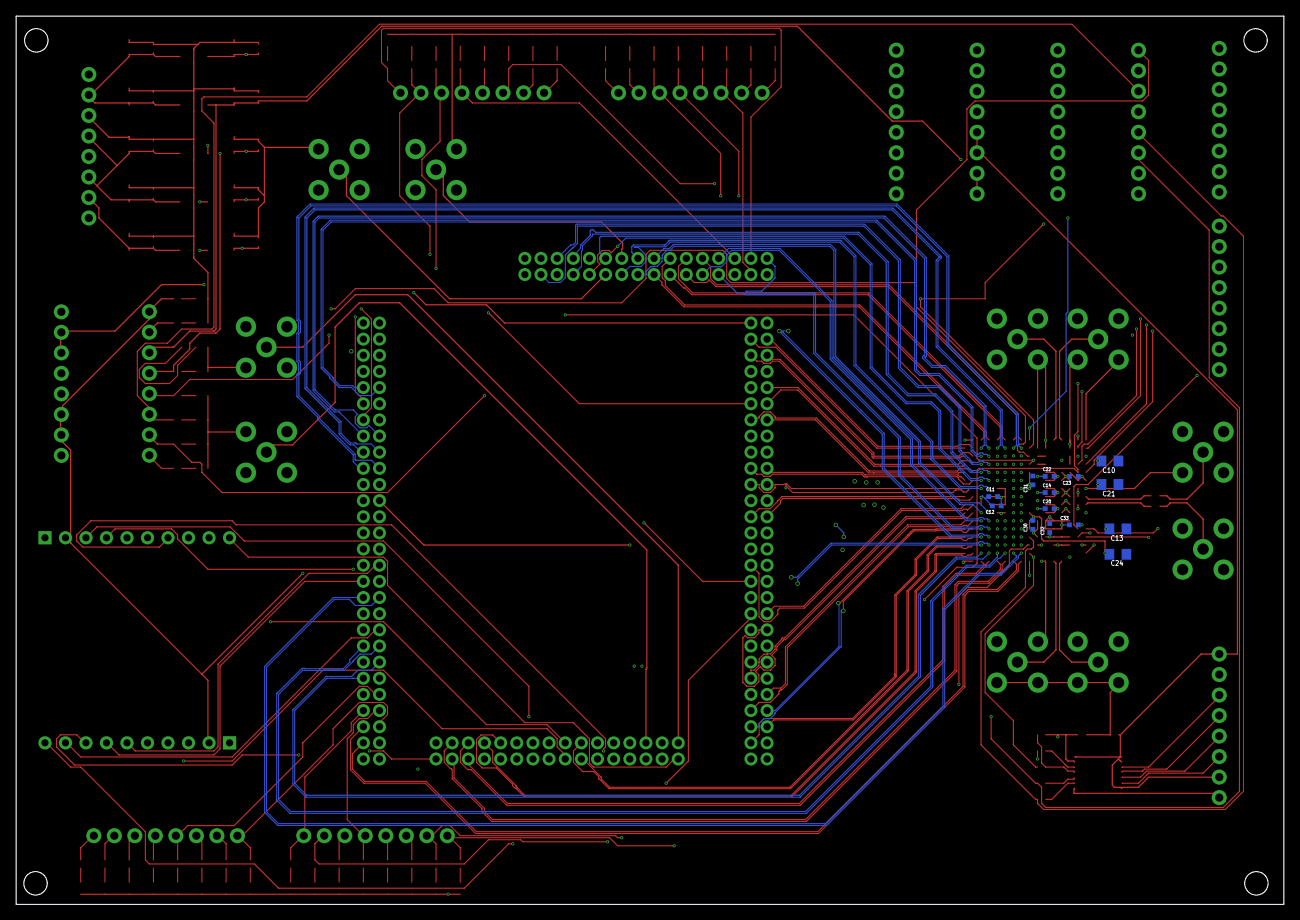
[picture p94: board haasoscope_pro_adc_board - no blind.brd from below]

Board: 10 copper layers, 157.0 x 110.0 mm, 164 parts (14 on the bottom side), 250 nets.
